Parin810/Farm-Produce-Logging-and-Monitoring-/Final Report/circuit.png

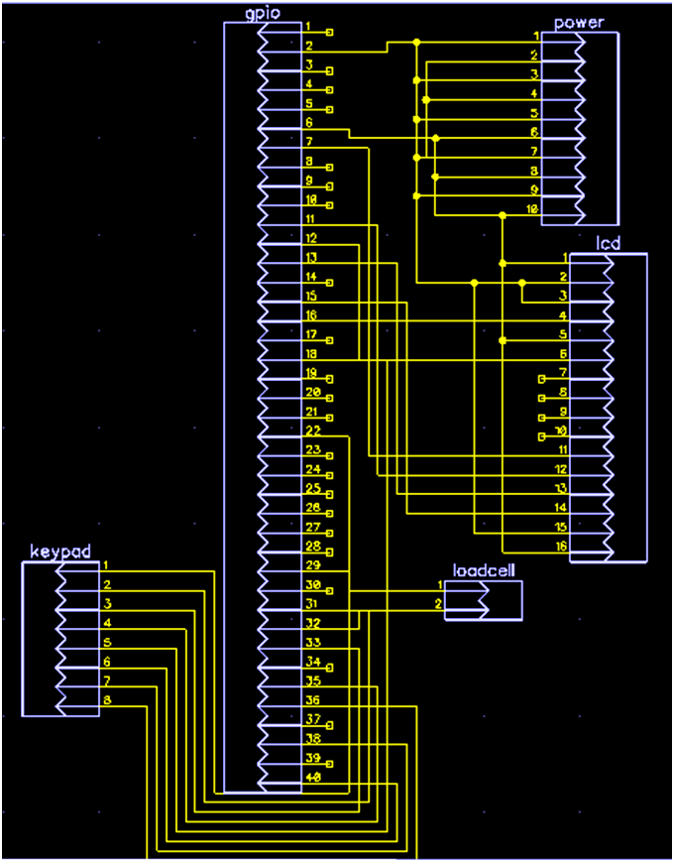
Final Report/circuit.png
