Parin810/Farm-Produce-Logging-and-Monitoring-/Poster/project_farmproduce.png

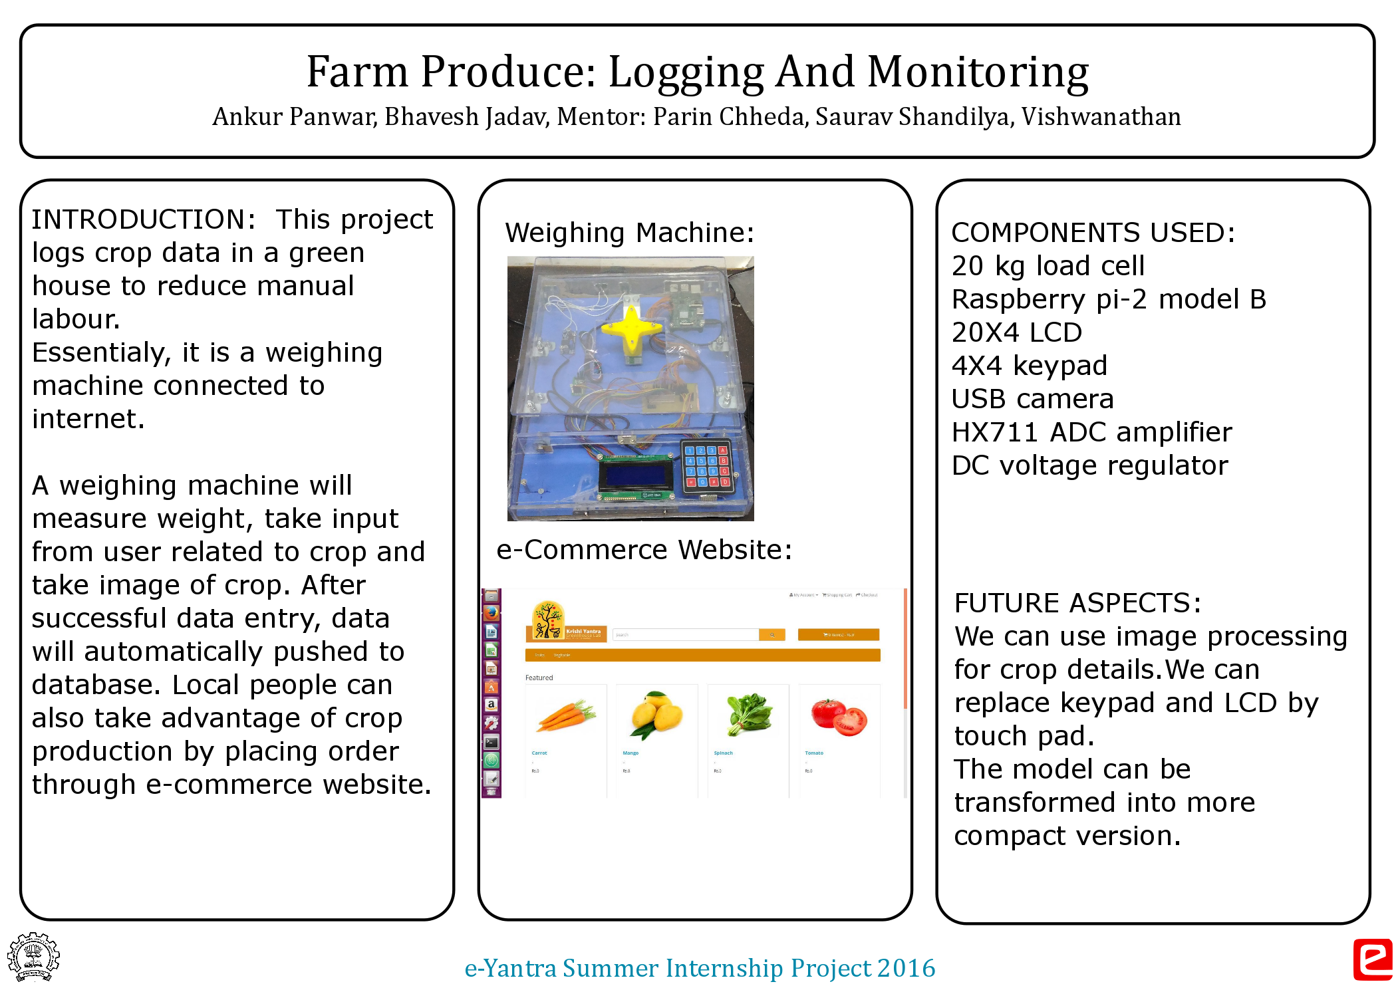
Poster/project_farmproduce.png
