Parin810/Farm-Produce-Logging-and-Monitoring-/progress-presentation-1/lcd.jpg

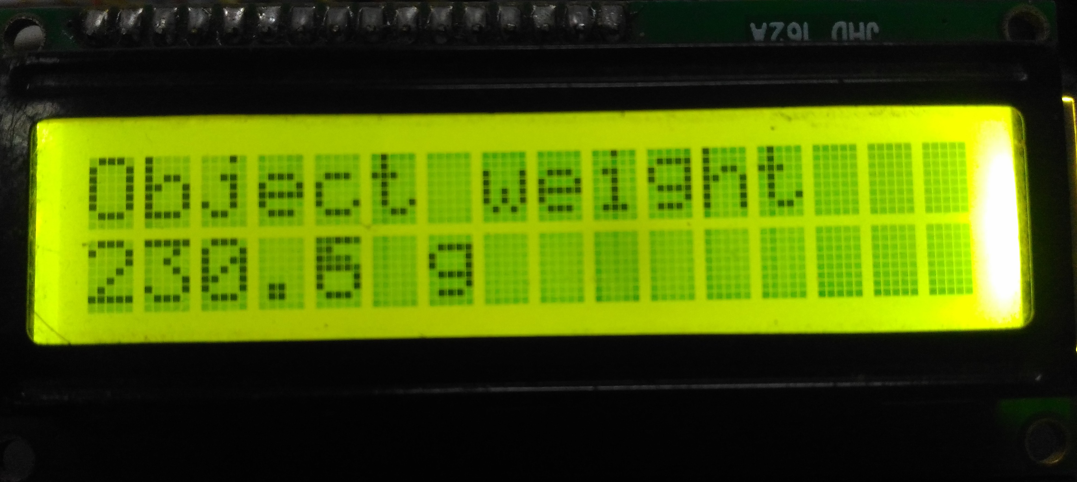
progress-presentation-1/lcd.jpg
