Parin810/Farm-Produce-Logging-and-Monitoring-/progress-presentation-1/load_cell.jpg

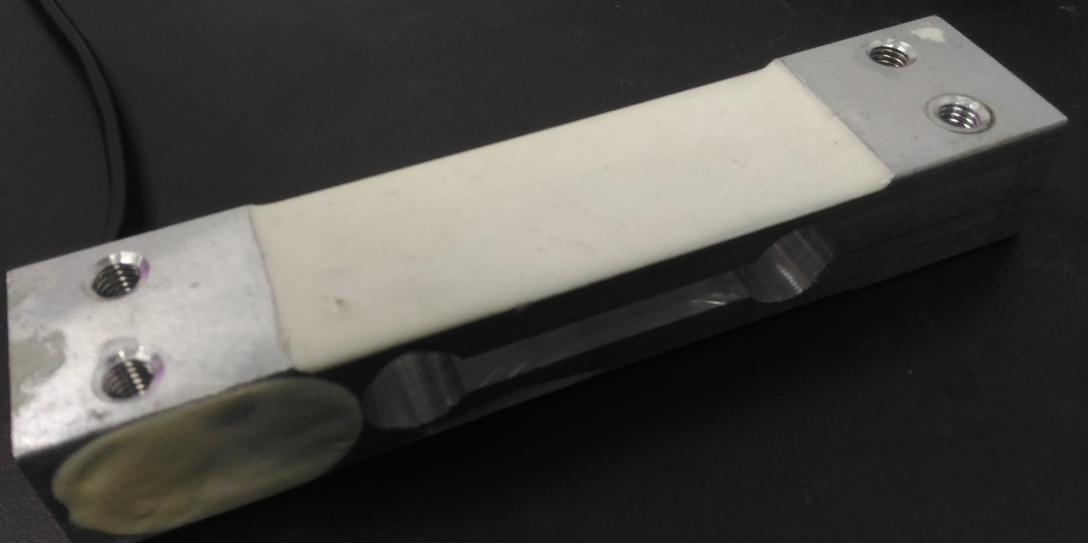
progress-presentation-1/load_cell.jpg
