Parin810/Farm-Produce-Logging-and-Monitoring-/progress-presentation-1/open.jpg

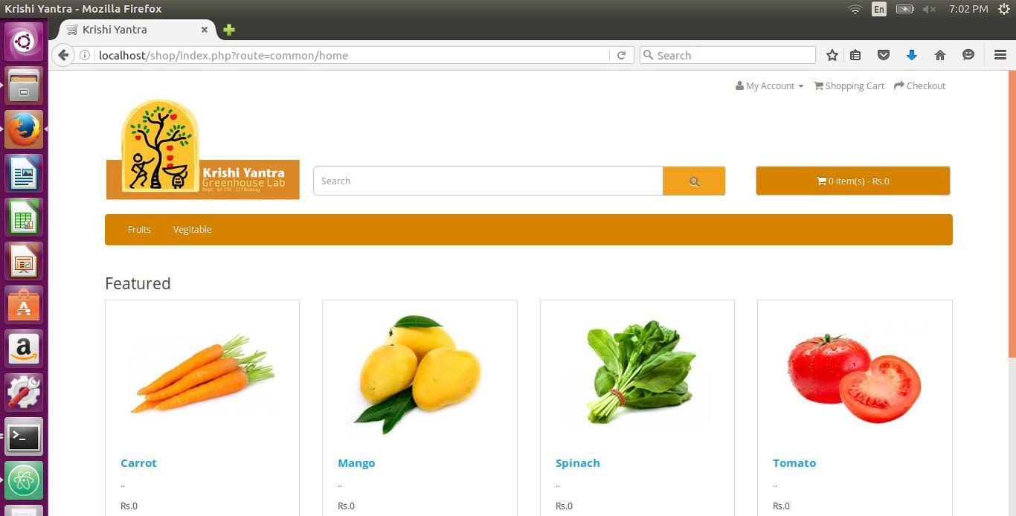
progress-presentation-1/open.jpg
