Parin810/Farm-Produce-Logging-and-Monitoring-/progress-presentation-1/page.jpg

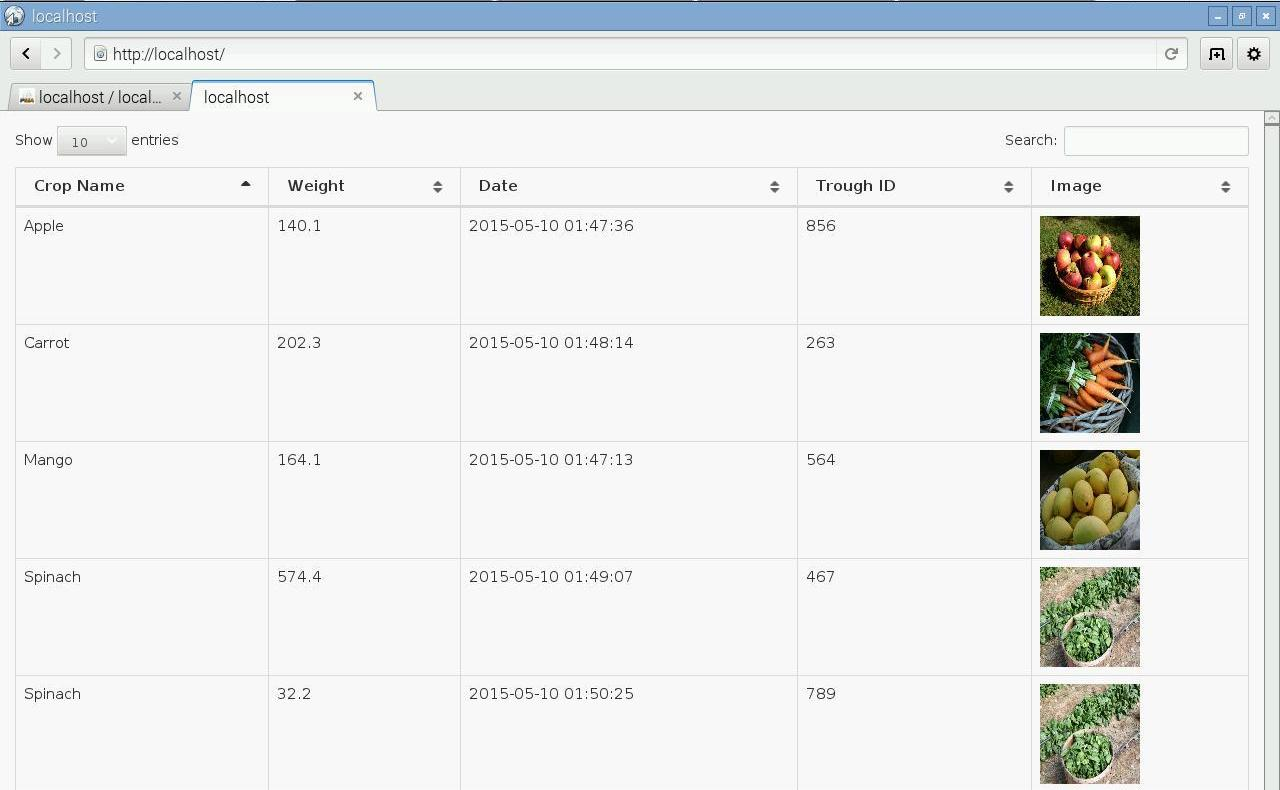
progress-presentation-1/page.jpg
