Parin810/Farm-Produce-Logging-and-Monitoring-/shop/admin/view/javascript/flot/examples/image/hs-2004-27-a-large-web.jpg

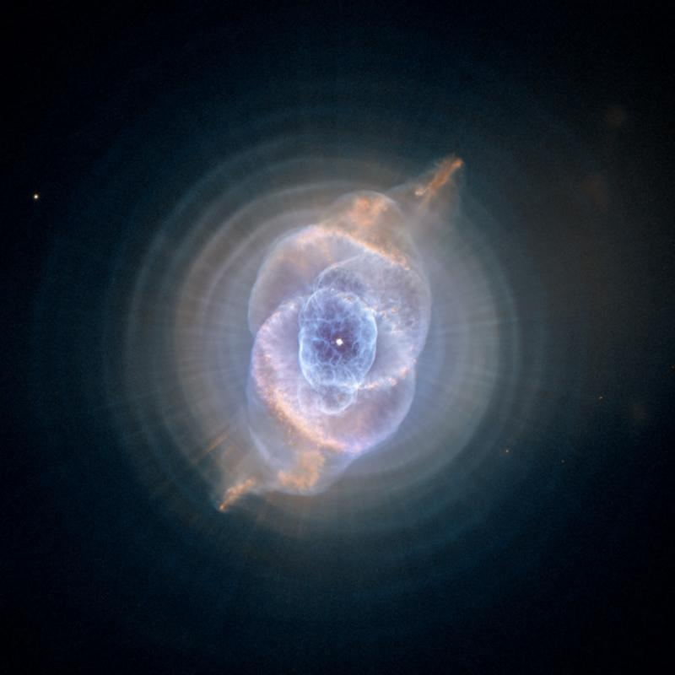
shop/admin/view/javascript/flot/examples/image/hs-2004-27-a-large-web.jpg
