Parin810/Farm-Produce-Logging-and-Monitoring-/shop/catalog/view/theme/default/image/default.png

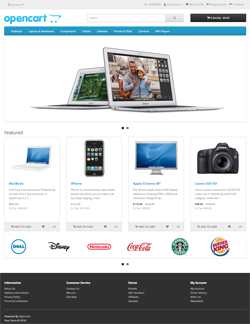
shop/catalog/view/theme/default/image/default.png
