Parin810/Farm-Produce-Logging-and-Monitoring-/shop/image/cache/catalog/demo/apple_cinema_30-200x200.jpg

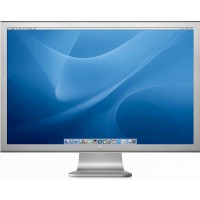
shop/image/cache/catalog/demo/apple_cinema_30-200x200.jpg
