Parin810/Farm-Produce-Logging-and-Monitoring-/shop/image/cache/catalog/demo/canon_eos_5d_1-200x200.jpg

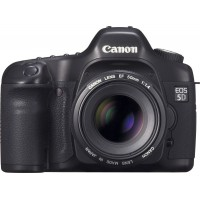
shop/image/cache/catalog/demo/canon_eos_5d_1-200x200.jpg
