Parin810/Farm-Produce-Logging-and-Monitoring-/shop/image/cache/catalog/demo/macbook_1-200x200.jpg

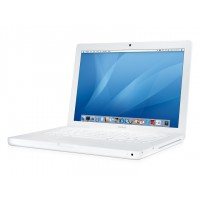
shop/image/cache/catalog/demo/macbook_1-200x200.jpg
