Parin810/Farm-Produce-Logging-and-Monitoring-/shop/image/cache/catalog/mango-200x200.jpeg

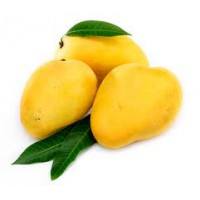
shop/image/cache/catalog/mango-200x200.jpeg
