Parin810/Farm-Produce-Logging-and-Monitoring-/shop/image/cache/catalog/spinach-200x200.jpg

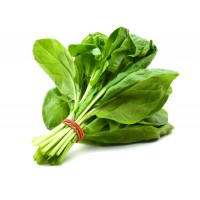
shop/image/cache/catalog/spinach-200x200.jpg
