Parin810/Farm-Produce-Logging-and-Monitoring-/shop/image/cache/placeholder-200x200.png

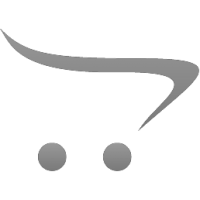
shop/image/cache/placeholder-200x200.png
