Parin810/Farm-Produce-Logging-and-Monitoring-/shop/image/catalog/carrot.jpg

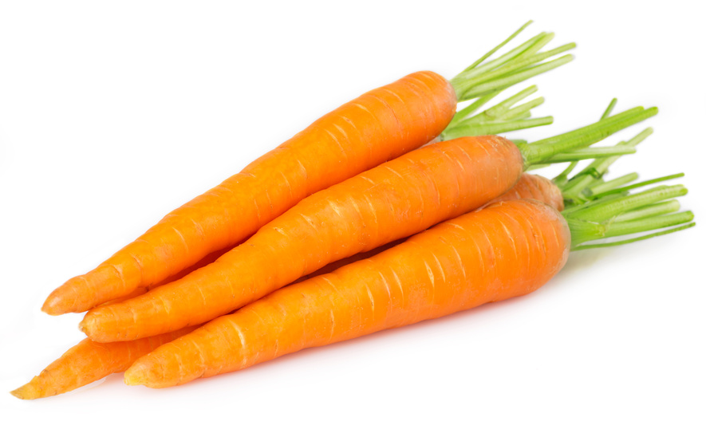
shop/image/catalog/carrot.jpg
