Parin810/Farm-Produce-Logging-and-Monitoring-/shop/image/catalog/demo/apple_cinema_30.jpg

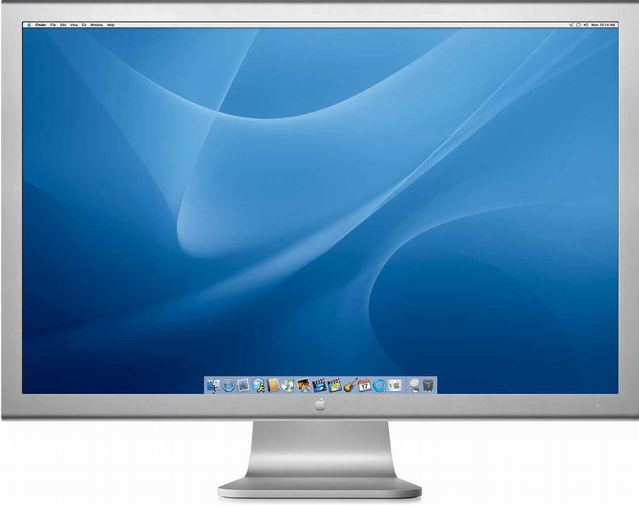
shop/image/catalog/demo/apple_cinema_30.jpg
