Parin810/Farm-Produce-Logging-and-Monitoring-/shop/image/catalog/demo/canon_eos_5d_2.jpg

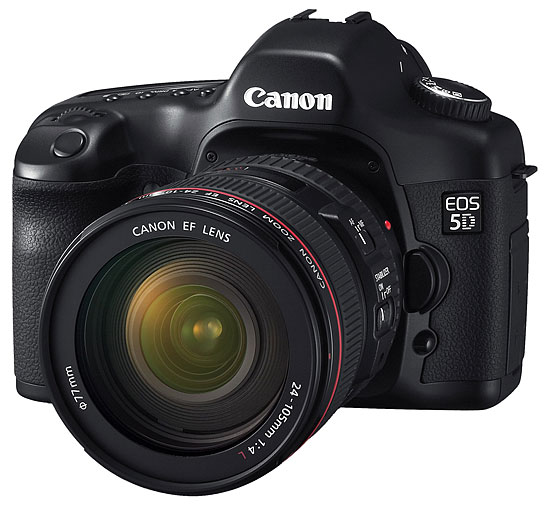
shop/image/catalog/demo/canon_eos_5d_2.jpg
