Parin810/Farm-Produce-Logging-and-Monitoring-/shop/image/catalog/demo/compaq_presario.jpg

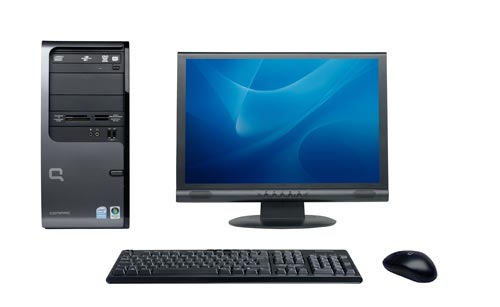
shop/image/catalog/demo/compaq_presario.jpg
