Parin810/Farm-Produce-Logging-and-Monitoring-/shop/image/catalog/demo/gift-voucher-birthday.jpg

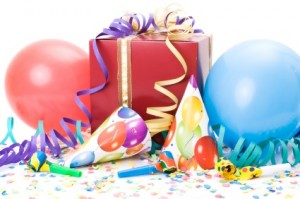
shop/image/catalog/demo/gift-voucher-birthday.jpg
