Parin810/Farm-Produce-Logging-and-Monitoring-/shop/image/catalog/demo/hp_1.jpg

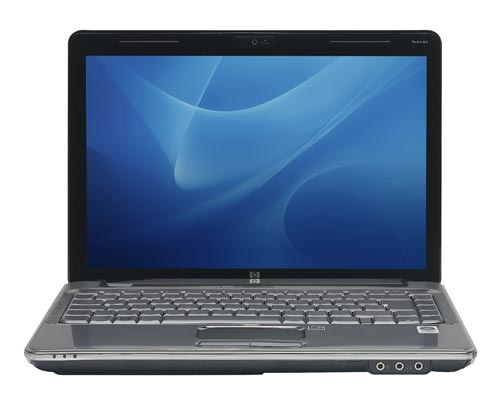
shop/image/catalog/demo/hp_1.jpg
