Parin810/Farm-Produce-Logging-and-Monitoring-/shop/image/catalog/demo/hp_2.jpg

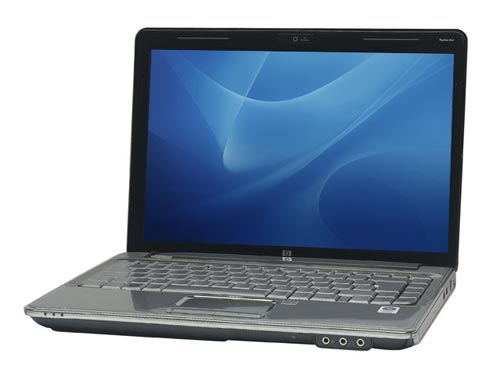
shop/image/catalog/demo/hp_2.jpg
