Parin810/Farm-Produce-Logging-and-Monitoring-/shop/image/catalog/demo/hp_3.jpg

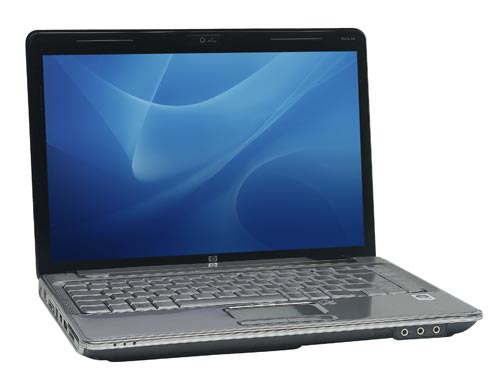
shop/image/catalog/demo/hp_3.jpg
