Parin810/Farm-Produce-Logging-and-Monitoring-/shop/image/catalog/demo/htc_touch_hd_1.jpg

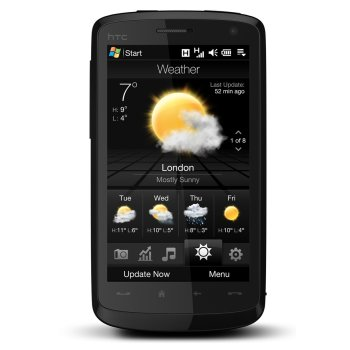
shop/image/catalog/demo/htc_touch_hd_1.jpg
