Parin810/Farm-Produce-Logging-and-Monitoring-/shop/image/catalog/demo/imac_1.jpg

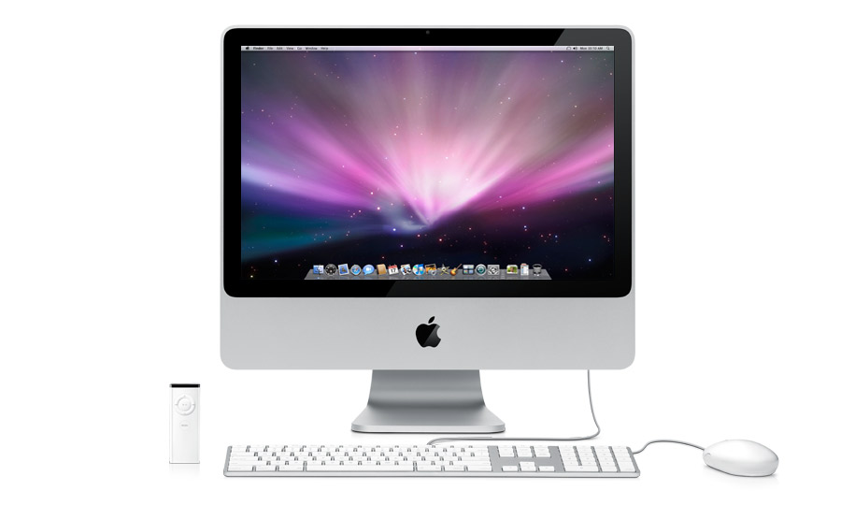
shop/image/catalog/demo/imac_1.jpg
