Parin810/Farm-Produce-Logging-and-Monitoring-/shop/image/catalog/demo/ipod_classic_3.jpg

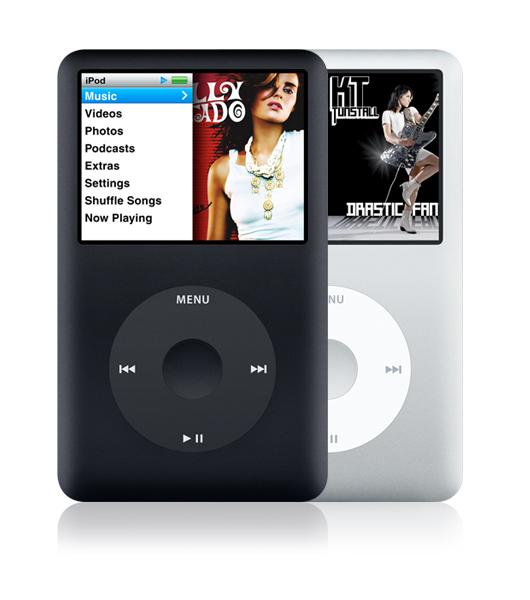
shop/image/catalog/demo/ipod_classic_3.jpg
