Parin810/Farm-Produce-Logging-and-Monitoring-/shop/image/catalog/demo/ipod_shuffle_1.jpg

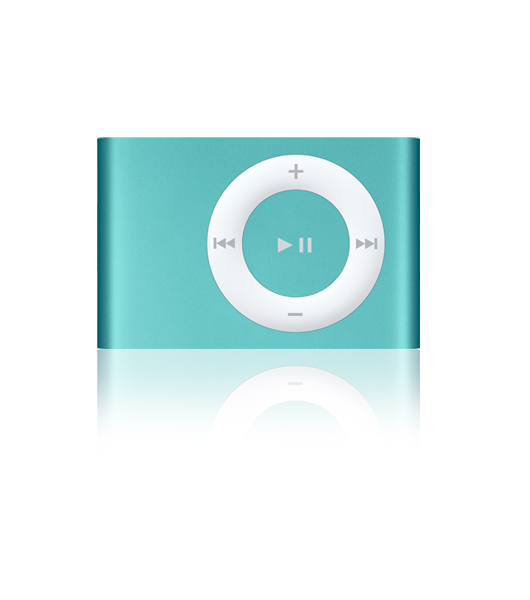
shop/image/catalog/demo/ipod_shuffle_1.jpg
