Parin810/Farm-Produce-Logging-and-Monitoring-/shop/image/catalog/demo/ipod_touch_4.jpg

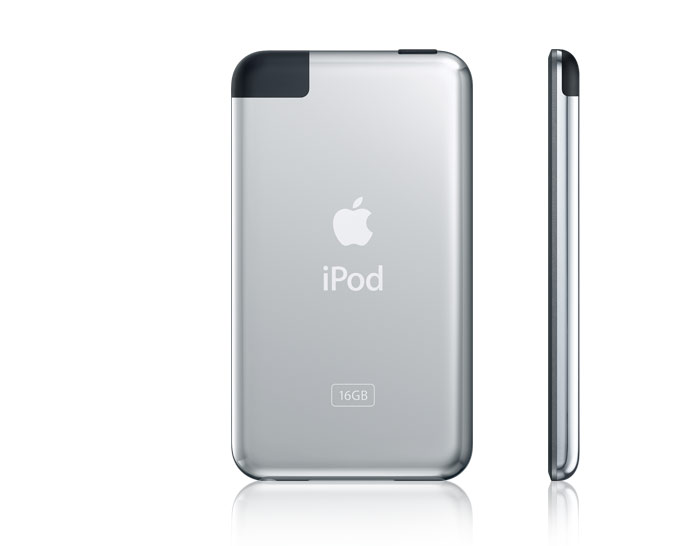
shop/image/catalog/demo/ipod_touch_4.jpg
