Parin810/Farm-Produce-Logging-and-Monitoring-/shop/image/catalog/demo/macbook_3.jpg

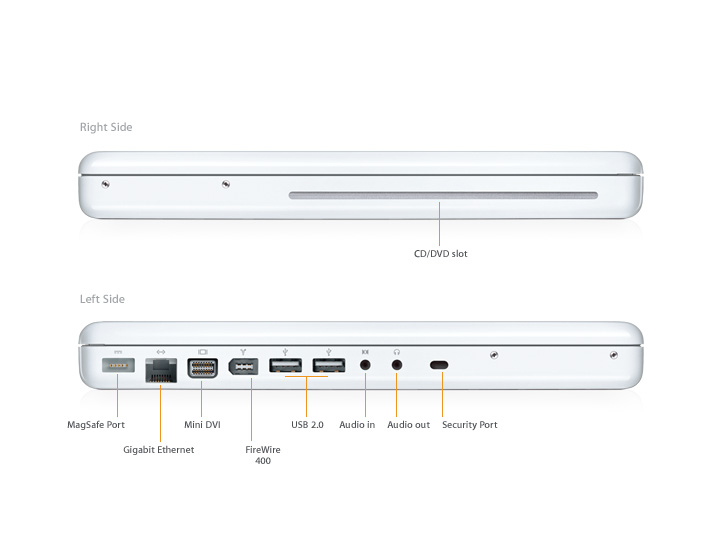
shop/image/catalog/demo/macbook_3.jpg
