Parin810/Farm-Produce-Logging-and-Monitoring-/shop/image/catalog/demo/macbook_4.jpg

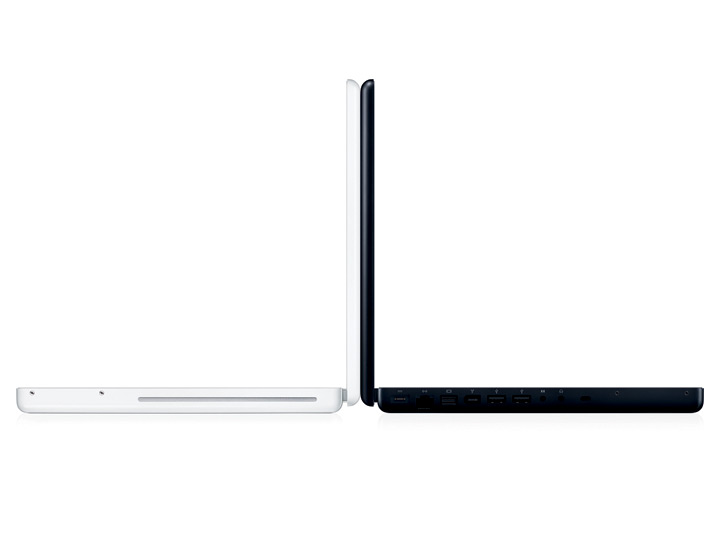
shop/image/catalog/demo/macbook_4.jpg
