Parin810/Farm-Produce-Logging-and-Monitoring-/shop/image/catalog/demo/macbook_air_2.jpg

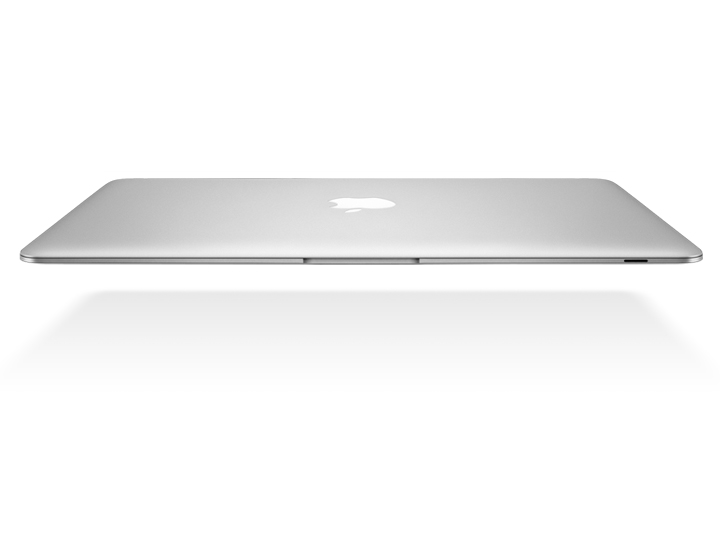
shop/image/catalog/demo/macbook_air_2.jpg
