Parin810/Farm-Produce-Logging-and-Monitoring-/shop/image/catalog/demo/macbook_air_3.jpg

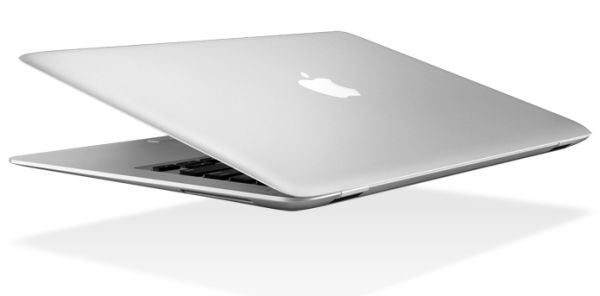
shop/image/catalog/demo/macbook_air_3.jpg
