Parin810/Farm-Produce-Logging-and-Monitoring-/shop/image/catalog/demo/macbook_pro_1.jpg

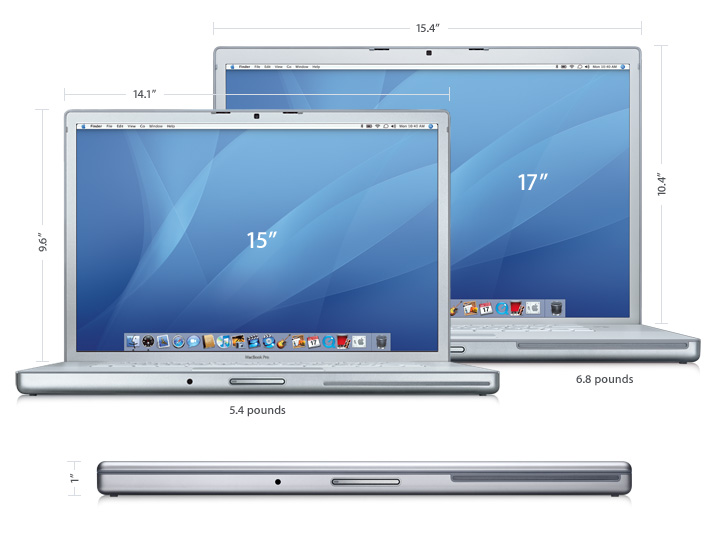
shop/image/catalog/demo/macbook_pro_1.jpg
