Parin810/Farm-Produce-Logging-and-Monitoring-/shop/image/catalog/demo/nikon_d300_3.jpg

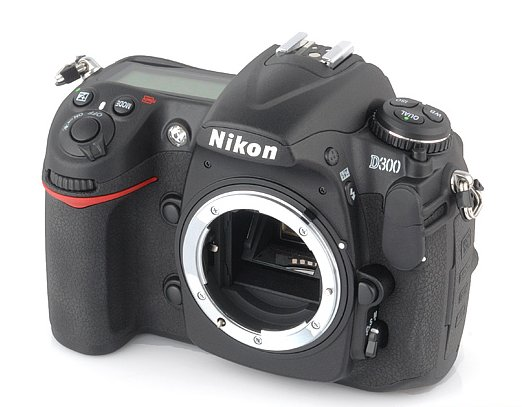
shop/image/catalog/demo/nikon_d300_3.jpg
