Parin810/Farm-Produce-Logging-and-Monitoring-/shop/image/catalog/demo/nikon_d300_4.jpg

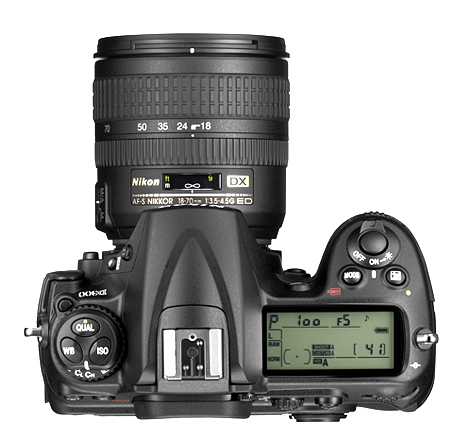
shop/image/catalog/demo/nikon_d300_4.jpg
