Parin810/Farm-Produce-Logging-and-Monitoring-/shop/image/catalog/demo/palm_treo_pro_2.jpg

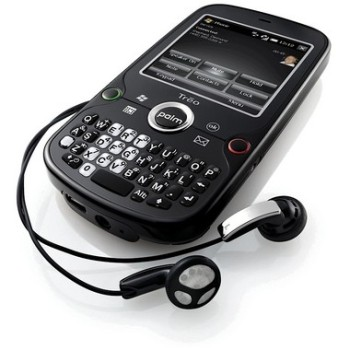
shop/image/catalog/demo/palm_treo_pro_2.jpg
