Parin810/Farm-Produce-Logging-and-Monitoring-/shop/image/catalog/demo/product/iphone.jpg

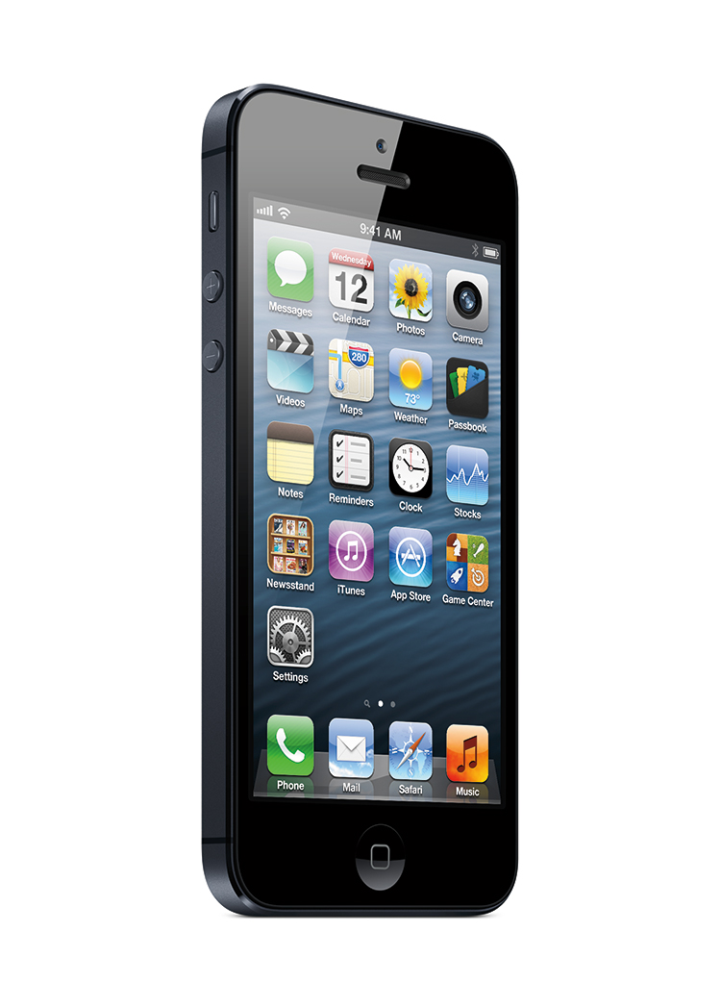
shop/image/catalog/demo/product/iphone.jpg
