Parin810/Farm-Produce-Logging-and-Monitoring-/shop/image/catalog/demo/product/macbook.jpg

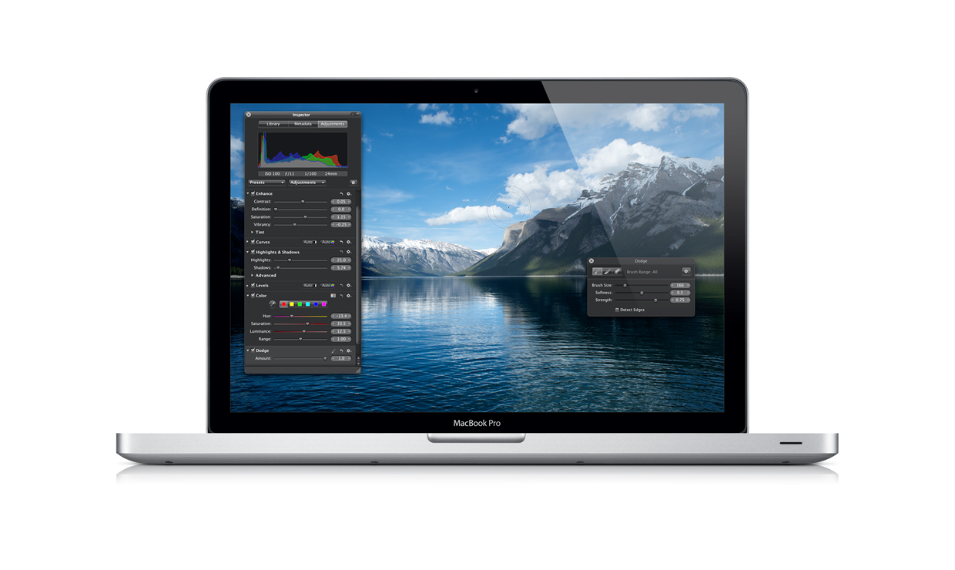
shop/image/catalog/demo/product/macbook.jpg
