Parin810/Farm-Produce-Logging-and-Monitoring-/shop/image/catalog/demo/product/samsungtab.jpg

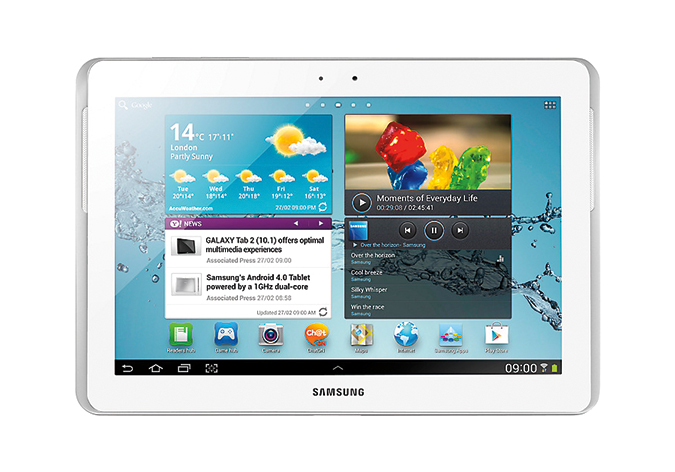
shop/image/catalog/demo/product/samsungtab.jpg
