Parin810/Farm-Produce-Logging-and-Monitoring-/shop/image/catalog/demo/product/thunderboltdisplay.jpg

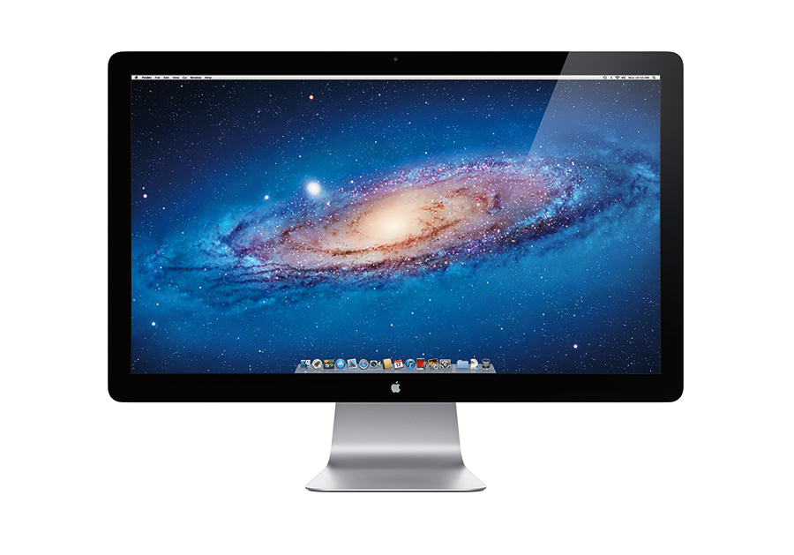
shop/image/catalog/demo/product/thunderboltdisplay.jpg
