Parin810/Farm-Produce-Logging-and-Monitoring-/shop/image/catalog/demo/samsung_syncmaster_941bw.jpg

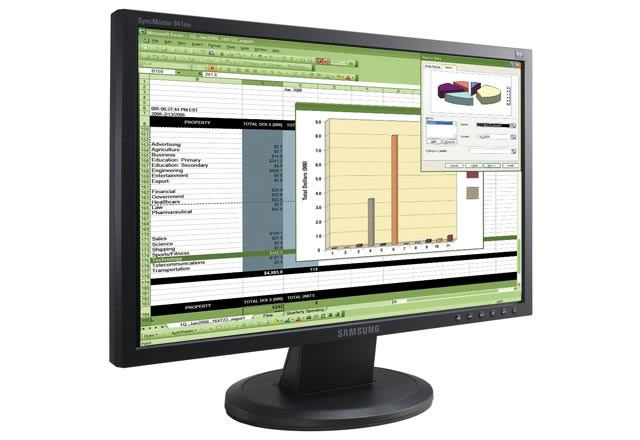
shop/image/catalog/demo/samsung_syncmaster_941bw.jpg
