Parin810/Farm-Produce-Logging-and-Monitoring-/shop/image/catalog/demo/samsung_tab_2.jpg

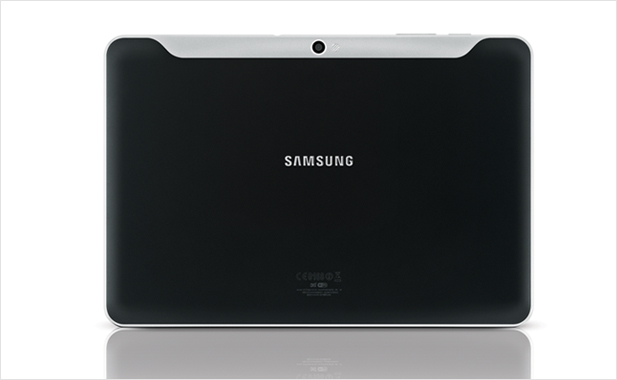
shop/image/catalog/demo/samsung_tab_2.jpg
