Parin810/Farm-Produce-Logging-and-Monitoring-/shop/image/catalog/demo/sony_vaio_2.jpg

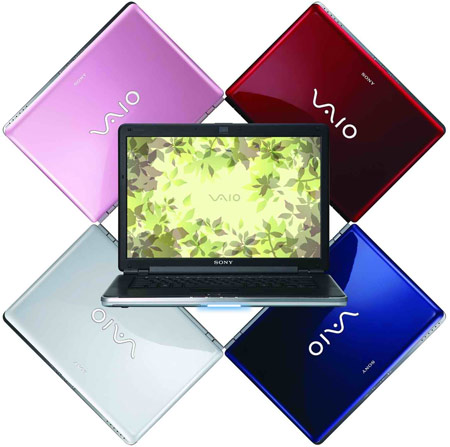
shop/image/catalog/demo/sony_vaio_2.jpg
