Parin810/Farm-Produce-Logging-and-Monitoring-/shop/image/catalog/KrishiYantra02.jpg

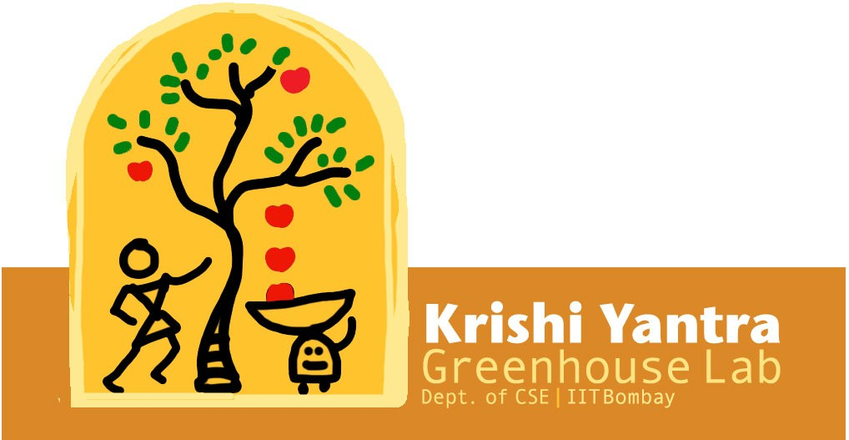
shop/image/catalog/KrishiYantra02.jpg
