Parin810/Farm-Produce-Logging-and-Monitoring-/shop/image/catalog/mango.jpeg

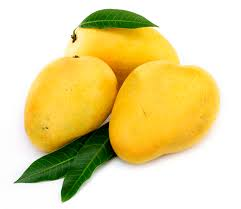
shop/image/catalog/mango.jpeg
