Parin810/Farm-Produce-Logging-and-Monitoring-/shop/image/catalog/spinach.jpg

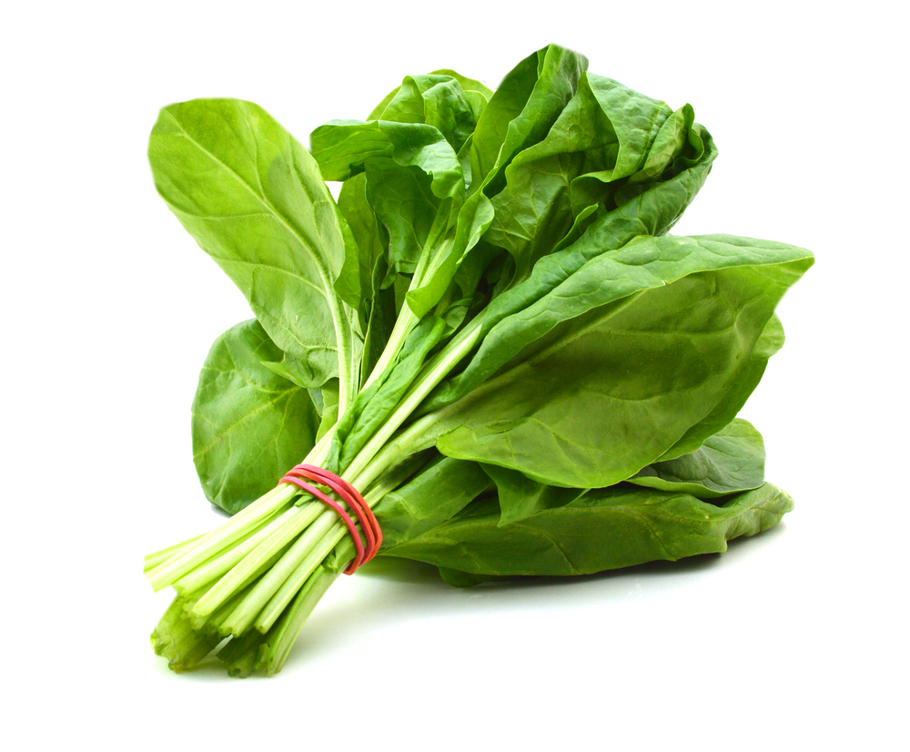
shop/image/catalog/spinach.jpg
