Parin810/Farm-Produce-Logging-and-Monitoring-/shop/image/catalog/tomato.jpeg

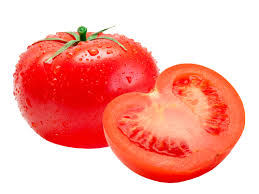
shop/image/catalog/tomato.jpeg
