Parin810/Farm-Produce-Logging-and-Monitoring-/shop/image/no_image.png

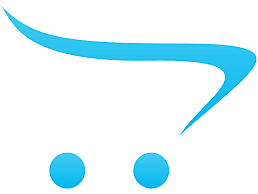
shop/image/no_image.png
