Parin810/Farm-Produce-Logging-and-Monitoring-/Weighing Machine Design/kpad/keypad-16keymembrane.jpg

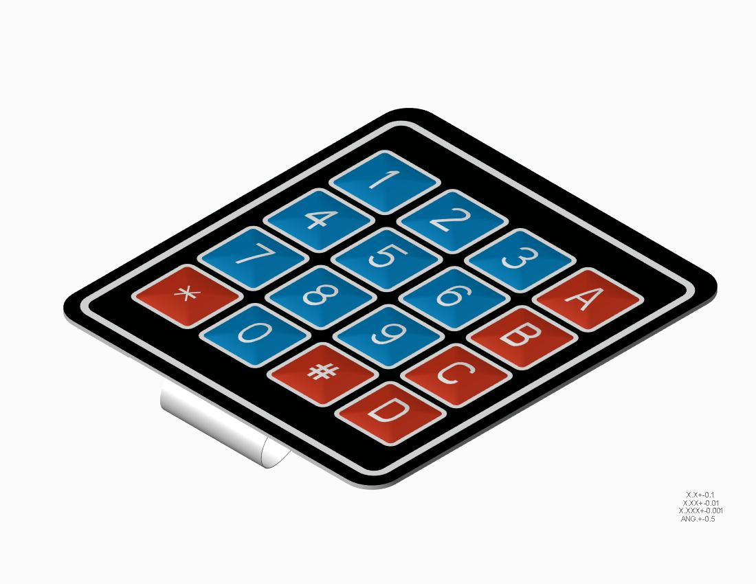
Weighing Machine Design/kpad/keypad-16keymembrane.jpg
