Parin810/Farm-Produce-Logging-and-Monitoring-/Weighing Machine Design/lcd/20X4LCD JHD204A.JPG

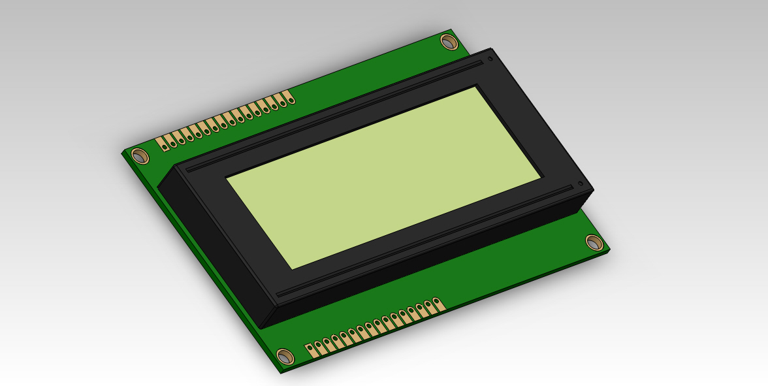
Weighing Machine Design/lcd/20X4LCD JHD204A.JPG
