Parin810/Farm-Produce-Logging-and-Monitoring-/Weighing Machine Design/pic1.JPG

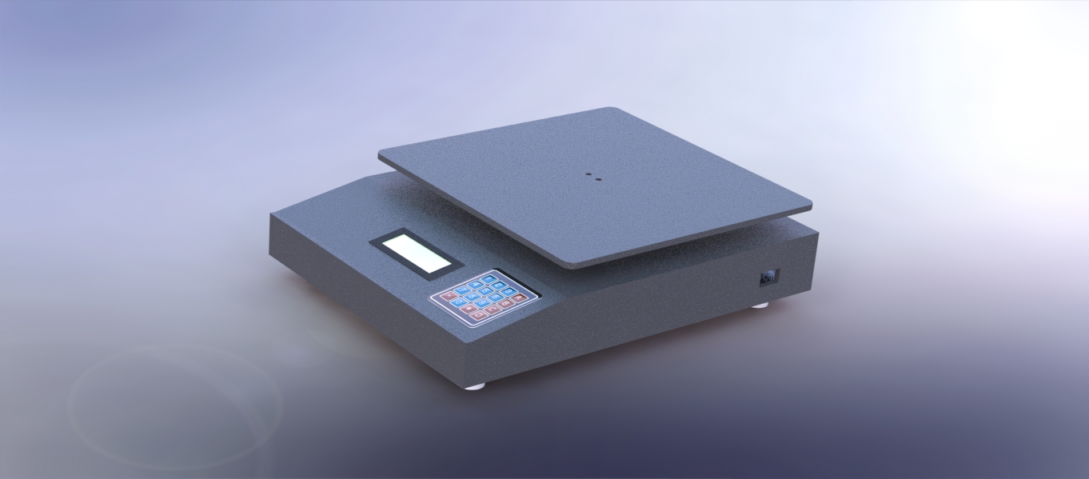
Weighing Machine Design/pic1.JPG
