Parin810/Farm-Produce-Logging-and-Monitoring-/Weighing Machine Design/pic2.JPG

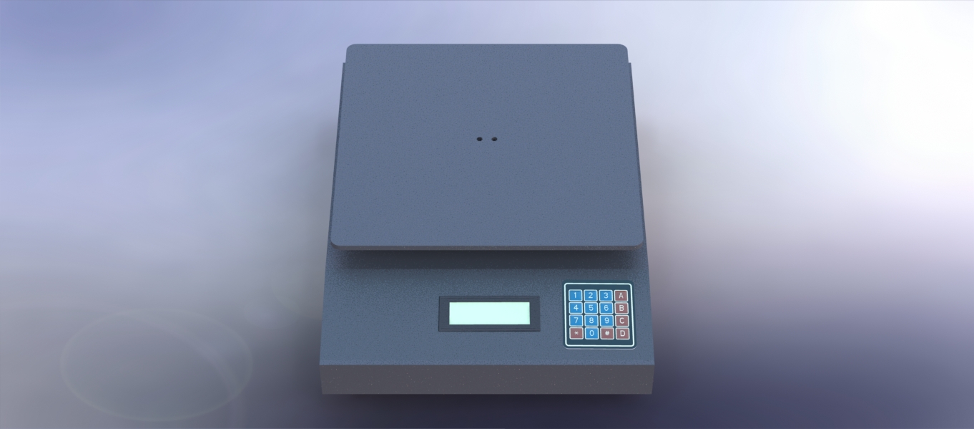
Weighing Machine Design/pic2.JPG
