Parin810/Farm-Produce-Logging-and-Monitoring-/Weighing Machine Design/pic3.JPG

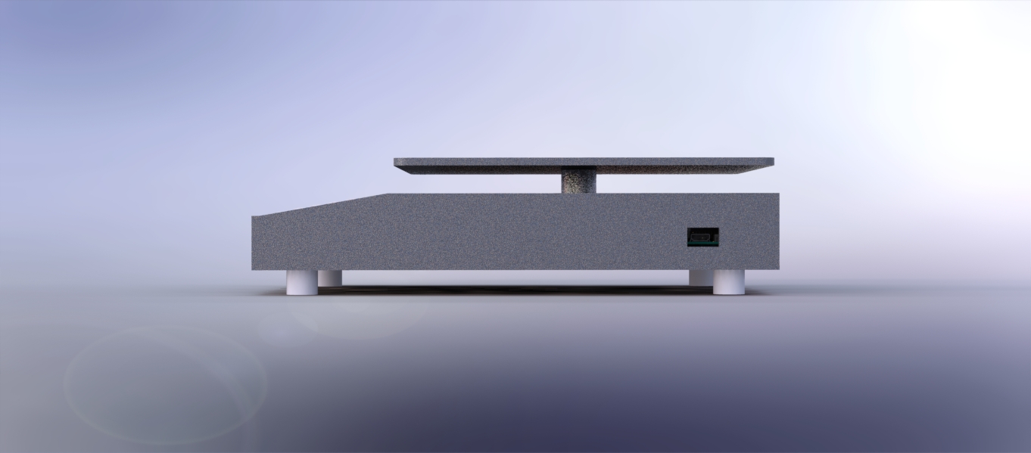
Weighing Machine Design/pic3.JPG
