Parin810/Farm-Produce-Logging-and-Monitoring-/Weighing Machine Design/pic4.JPG

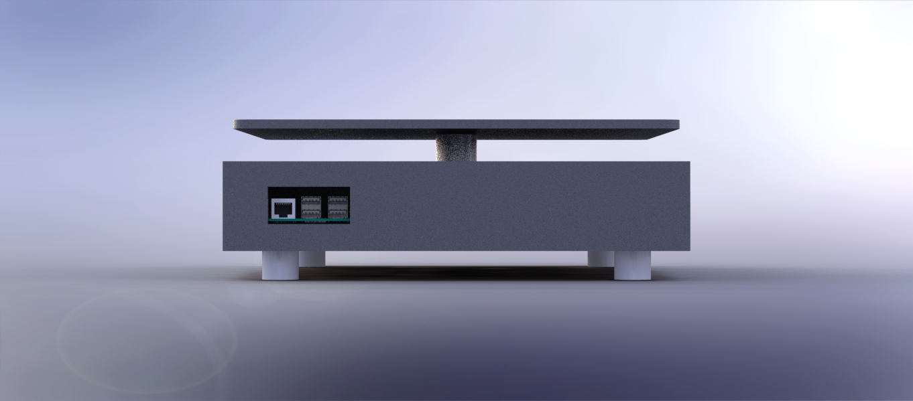
Weighing Machine Design/pic4.JPG
