Parin810/Farm-Produce-Logging-and-Monitoring-/Weighing Machine Design/pic5.JPG

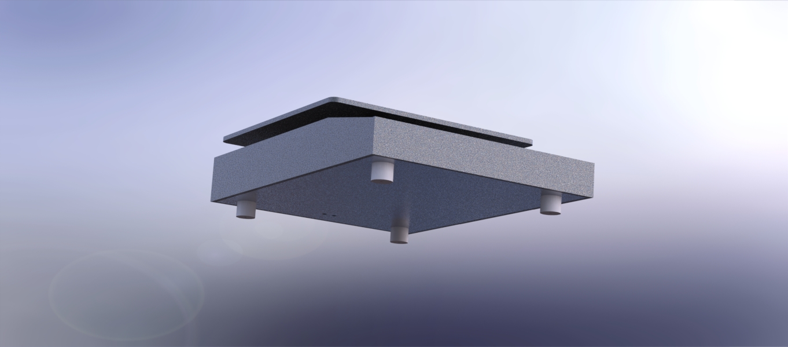
Weighing Machine Design/pic5.JPG
