Parin810/Farm-Produce-Logging-and-Monitoring-/Weighing Machine Design/rpi/@raspberry_pi_model_B+_bot_2.jpg

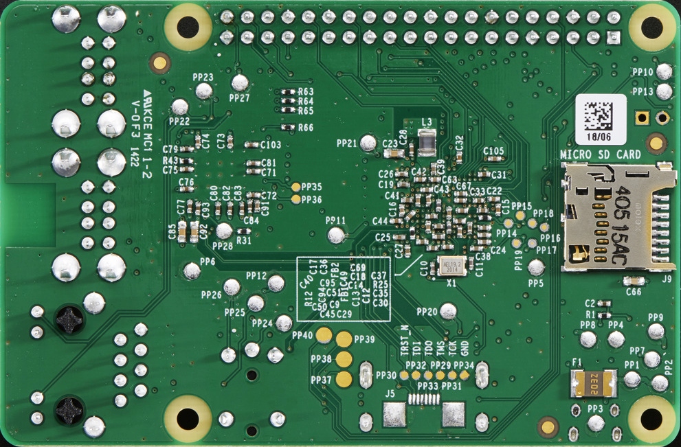
Weighing Machine Design/rpi/@raspberry_pi_model_B+_bot_2.jpg
