Parin810/Farm-Produce-Logging-and-Monitoring-/Weighing Machine Design/rpi/@raspberry_pi_model_B+_top_1.jpg

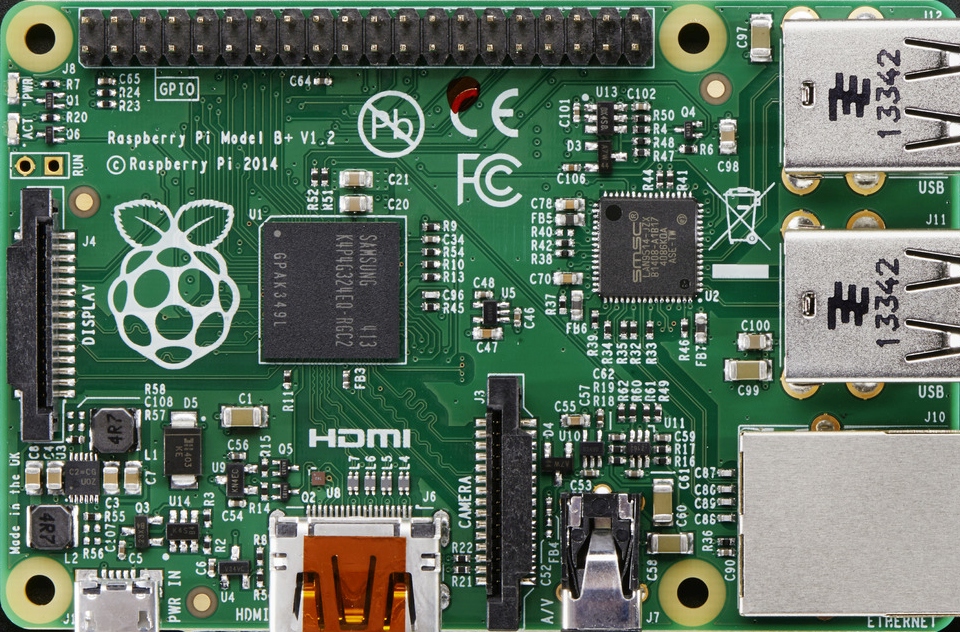
Weighing Machine Design/rpi/@raspberry_pi_model_B+_top_1.jpg
