Parin810/Farm-Produce-Logging-and-Monitoring-/Weighing Machine Design/rpi/mechanicalspecB+.png

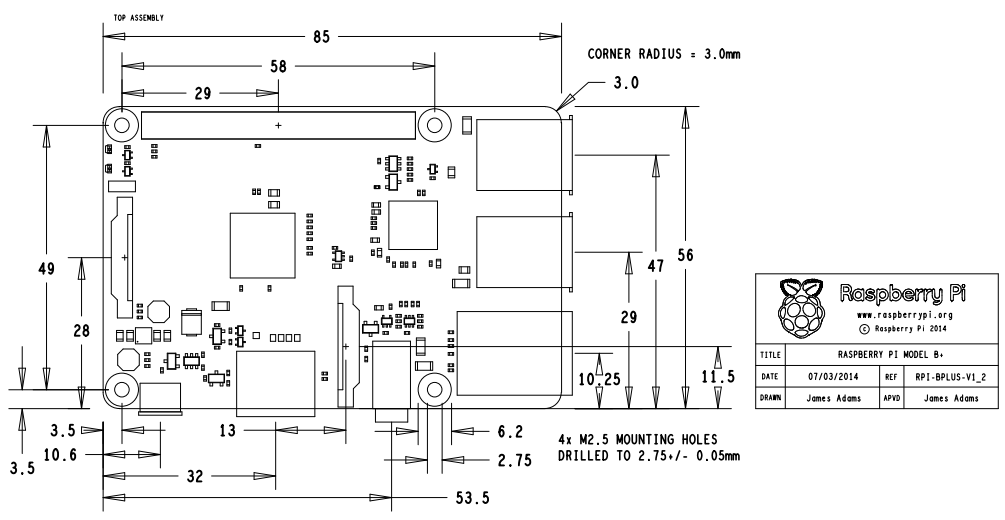
Weighing Machine Design/rpi/mechanicalspecB+.png
