Parin810/Farm-Produce-Logging-and-Monitoring-/Weighing Machine Design/rpi/raspberry_pi_B+_(RENDER2).JPG

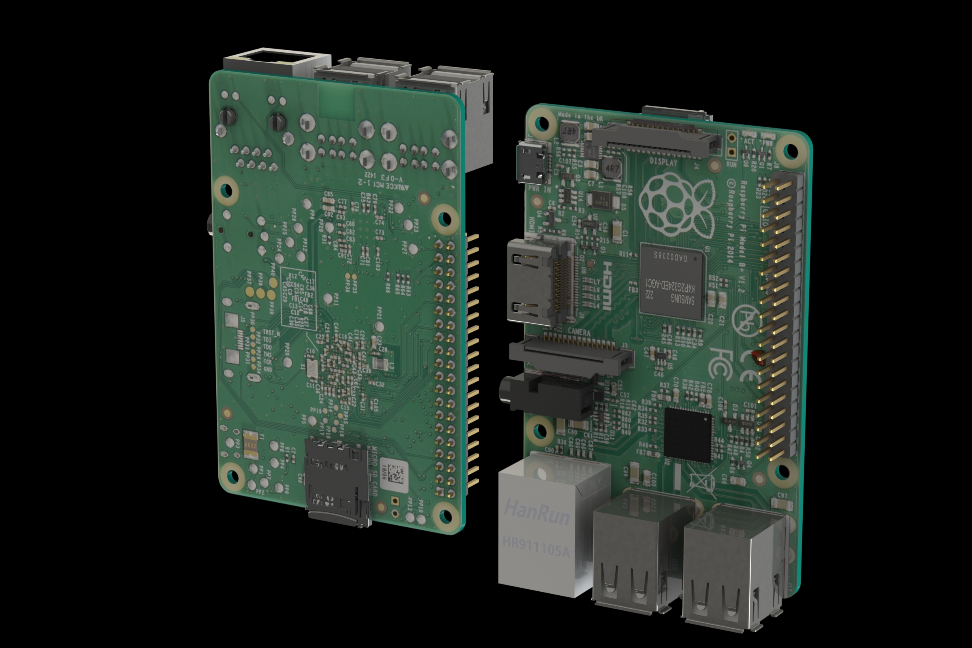
Weighing Machine Design/rpi/raspberry_pi_B+_(RENDER2).JPG
