Parin810/Farm-Produce-Logging-and-Monitoring-/Weighing Machine Design/lasercut/plate3.DXF

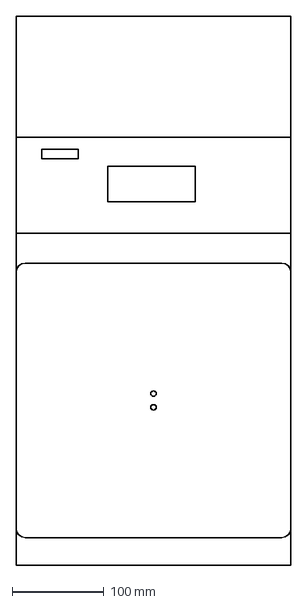
[picture p157: CAD file, 2017-04-19]
Weighing Machine Design/lasercut/plate3.DXF
300.0 x 600.0 mm
