Parin810/Farm-Produce-Logging-and-Monitoring-/Weighing Machine Design/lcd/20X4LCD JHD204A.STEP

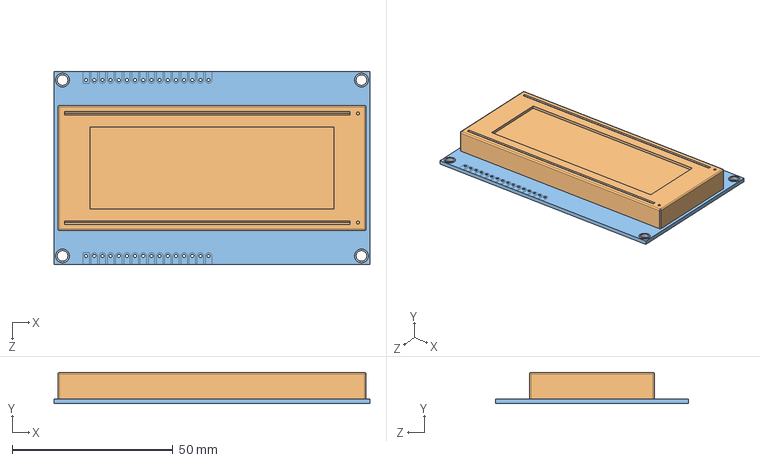
[picture p158: CAD file, 2017-04-19]
Weighing Machine Design/lcd/20X4LCD JHD204A.STEP
98.3 x 9.76 x 60.0 mm
