Parin810/Farm-Produce-Logging-and-Monitoring-/Weighing Machine Design/loadcell.SLDPRT

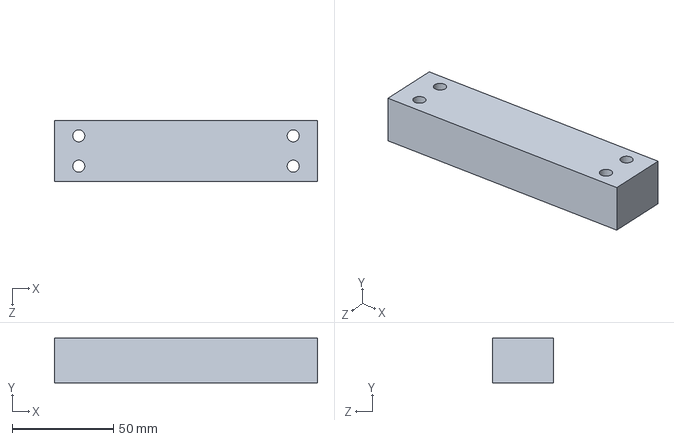
[picture p159: CAD file, 2017-04-19]
Weighing Machine Design/loadcell.SLDPRT
130.0 x 22.0 x 30.0 mm
