Parin810/Farm-Produce-Logging-and-Monitoring-/Weighing Machine Design/frontpanelcut.SLDPRT

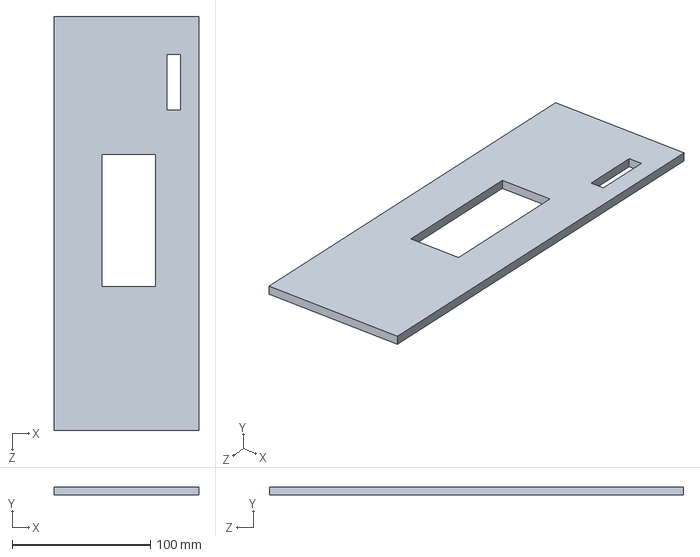
[picture p160: CAD file, 2017-04-19]
Weighing Machine Design/frontpanelcut.SLDPRT
105.0 x 6.00 x 300.0 mm
