Parin810/Farm-Produce-Logging-and-Monitoring-/Weighing Machine Design/lasercut/plate1.DXF

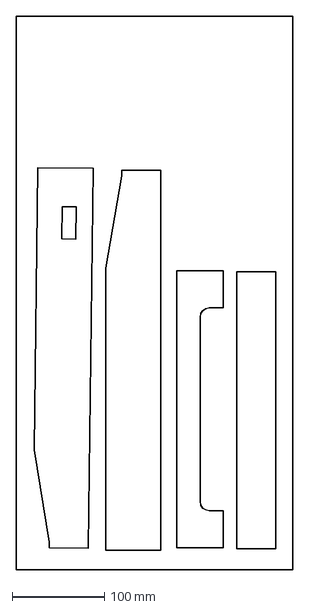
[picture p161: CAD file, 2017-04-19]
Weighing Machine Design/lasercut/plate1.DXF
300.0 x 600.0 mm
