Parin810/Farm-Produce-Logging-and-Monitoring-/Weighing Machine Design/rpi/raspberry_pi_B+_(audio_video2).SLDPRT

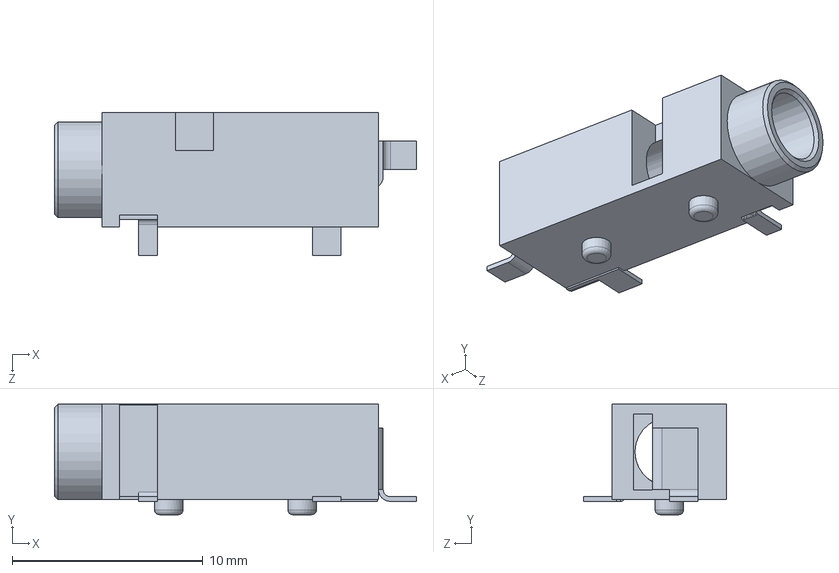
[picture p163: CAD file, 2017-04-19]
Weighing Machine Design/rpi/raspberry_pi_B+_(audio_video2).SLDPRT
19.0 x 5.80 x 7.50 mm
