Parin810/Farm-Produce-Logging-and-Monitoring-/Weighing Machine Design/rpi/raspberry_pi_B+_(RJ45).SLDPRT

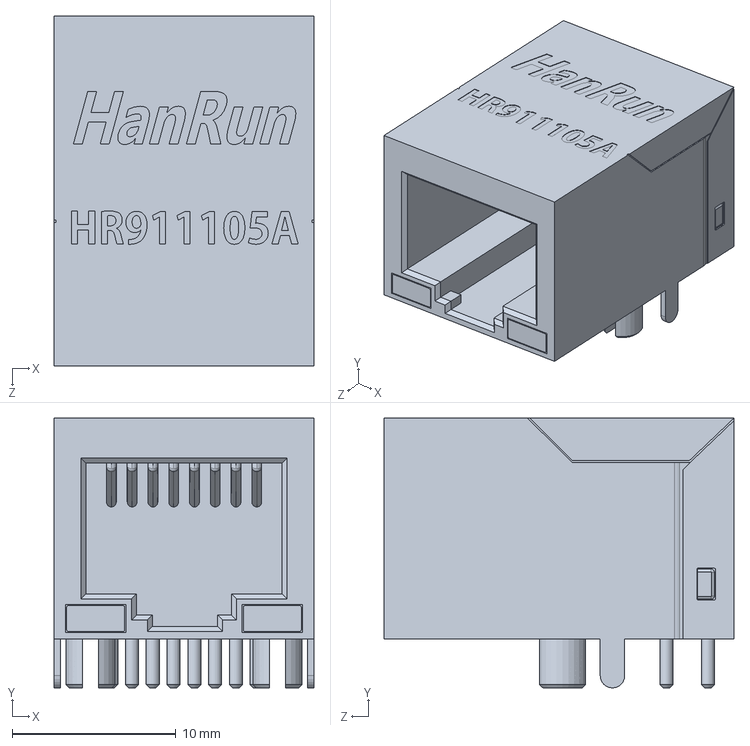
[picture p164: CAD file, 2017-04-19]
Weighing Machine Design/rpi/raspberry_pi_B+_(RJ45).SLDPRT
15.9 x 16.5 x 21.4 mm
