Parin810/Farm-Produce-Logging-and-Monitoring-/Weighing Machine Design/sidepanels2.SLDPRT

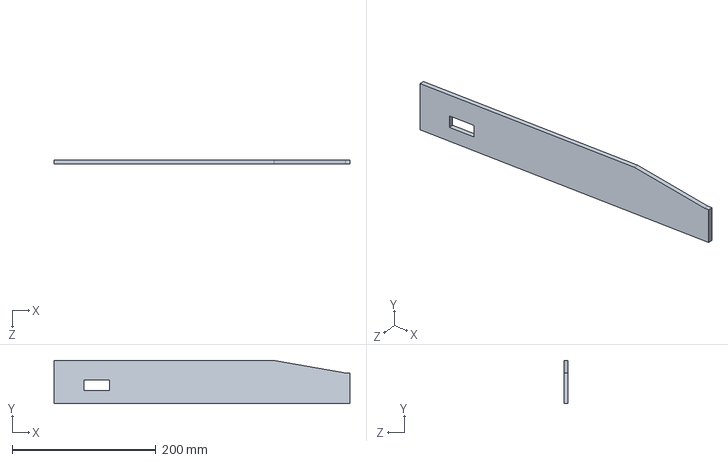
[picture p166: CAD file, 2017-04-19]
Weighing Machine Design/sidepanels2.SLDPRT
412.0 x 60.0 x 6.00 mm
