Parin810/Farm-Produce-Logging-and-Monitoring-/Weighing Machine Design/FrontPanel.SLDPRT

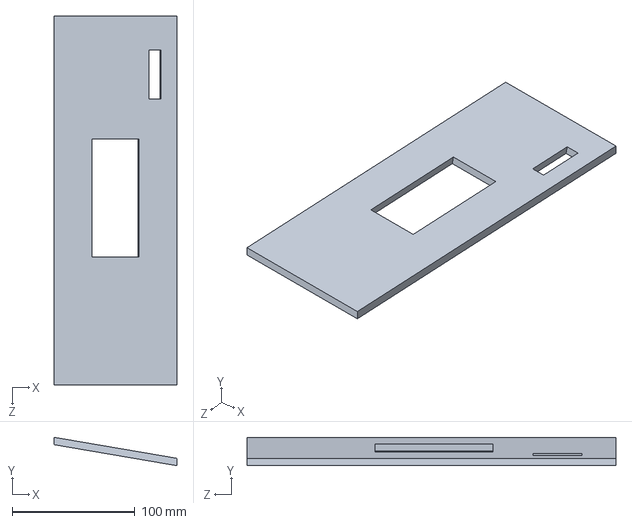
[picture p167: CAD file, 2017-04-19]
Weighing Machine Design/FrontPanel.SLDPRT
100.0 x 23.1 x 300.0 mm
