Parin810/Farm-Produce-Logging-and-Monitoring-/Weighing Machine Design/rpi/raspberry_pi_B+_(168_FBGA_12x12).SLDPRT

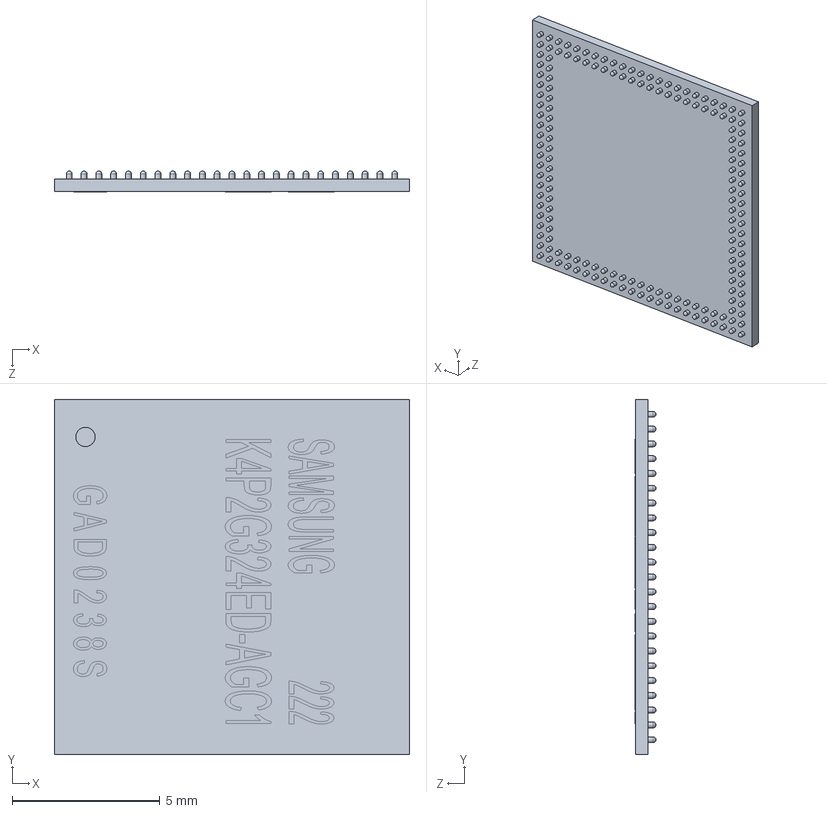
[picture p168: CAD file, 2017-04-19]
Weighing Machine Design/rpi/raspberry_pi_B+_(168_FBGA_12x12).SLDPRT
12.0 x 12.0 x 0.71 mm
