Parin810/Farm-Produce-Logging-and-Monitoring-/Weighing Machine Design/basecylinder.SLDPRT

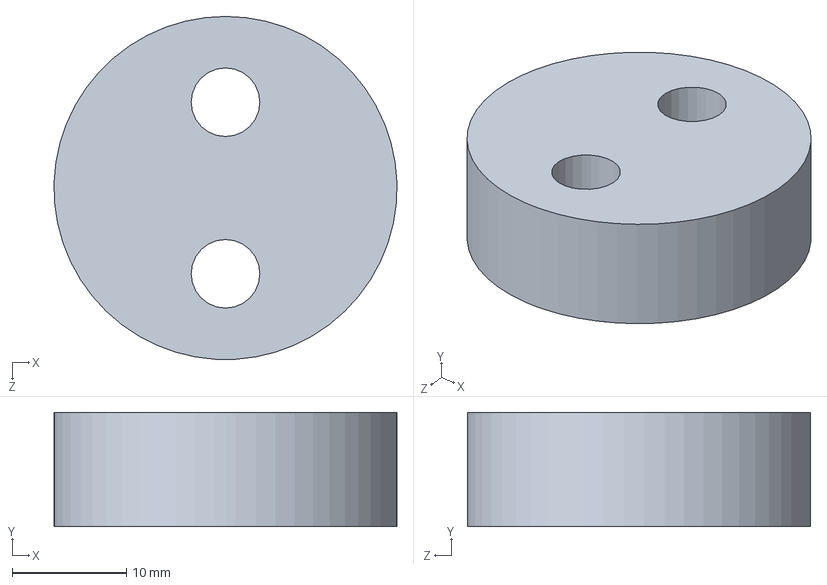
[picture p169: CAD file, 2017-04-19]
Weighing Machine Design/basecylinder.SLDPRT
30.0 x 10.0 x 30.0 mm
