Parin810/Farm-Produce-Logging-and-Monitoring-/Weighing Machine Design/rpi/raspberry_pi_B+_(CI_Board).SLDPRT

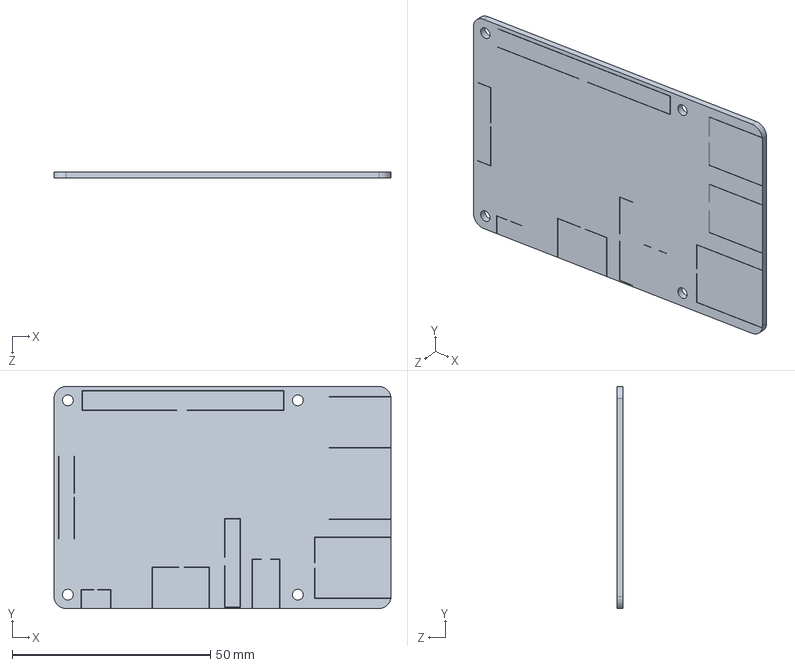
[picture p170: CAD file, 2017-04-19]
Weighing Machine Design/rpi/raspberry_pi_B+_(CI_Board).SLDPRT
85.0 x 56.0 x 1.60 mm
