Parin810/Farm-Produce-Logging-and-Monitoring-/Weighing Machine Design/rpi/raspberry_pi_B+_(microsd2).SLDPRT

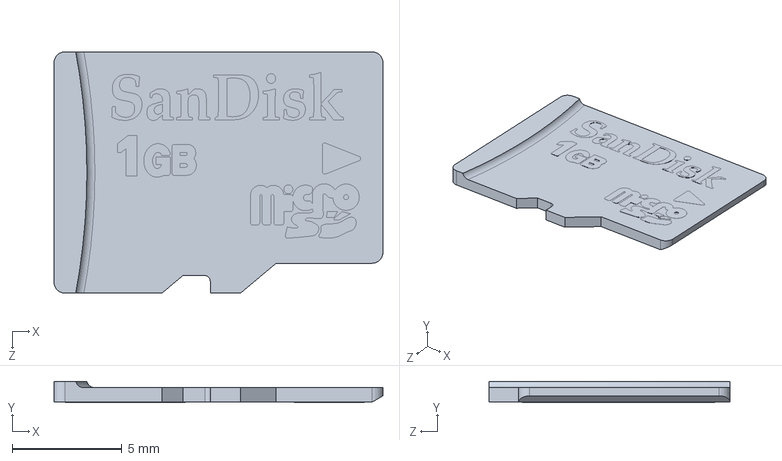
[picture p171: CAD file, 2017-04-19]
Weighing Machine Design/rpi/raspberry_pi_B+_(microsd2).SLDPRT
15.0 x 0.975 x 11.0 mm
