Parin810/Farm-Produce-Logging-and-Monitoring-/Weighing Machine Design/rpi/raspberry_pi__HDMI_socket_large_pin.SLDPRT

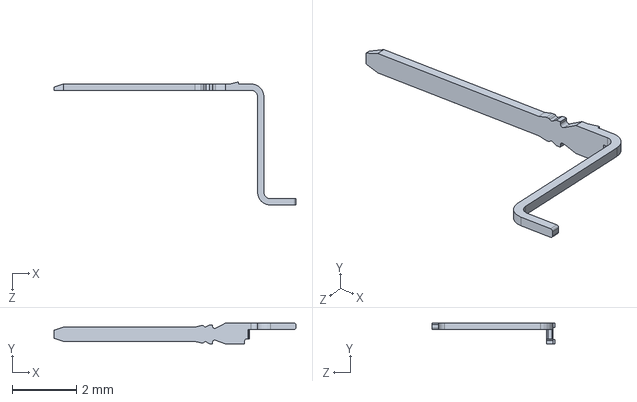
[picture p172: CAD file, 2017-04-19]
Weighing Machine Design/rpi/raspberry_pi__HDMI_socket_large_pin.SLDPRT
7.55 x 0.65 x 3.84 mm
