Parin810/Farm-Produce-Logging-and-Monitoring-/Weighing Machine Design/rpi/raspberry_pi_B+_(QFN64).SLDPRT

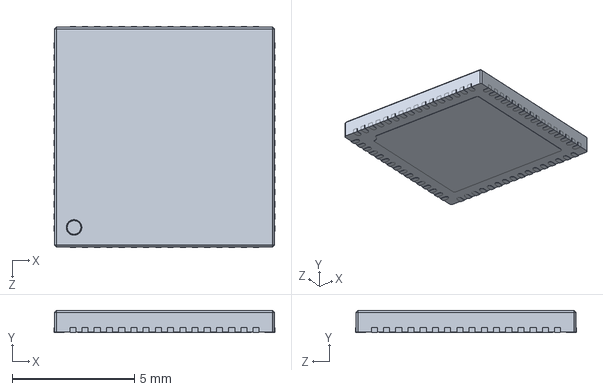
[picture p173: CAD file, 2017-04-19]
Weighing Machine Design/rpi/raspberry_pi_B+_(QFN64).SLDPRT
9.04 x 0.9 x 9.04 mm
