Parin810/Farm-Produce-Logging-and-Monitoring-/Weighing Machine Design/WeighingPlateform.SLDPRT

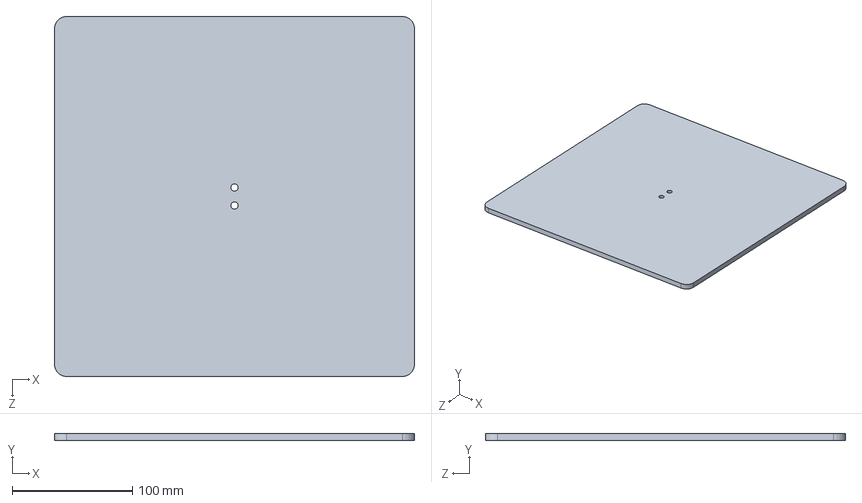
[picture p174: CAD file, 2017-04-19]
Weighing Machine Design/WeighingPlateform.SLDPRT
300.0 x 6.00 x 300.0 mm
