Parin810/Farm-Produce-Logging-and-Monitoring-/Weighing Machine Design/rpi/raspberry_pi_B+_(bar_180_2x20).SLDPRT

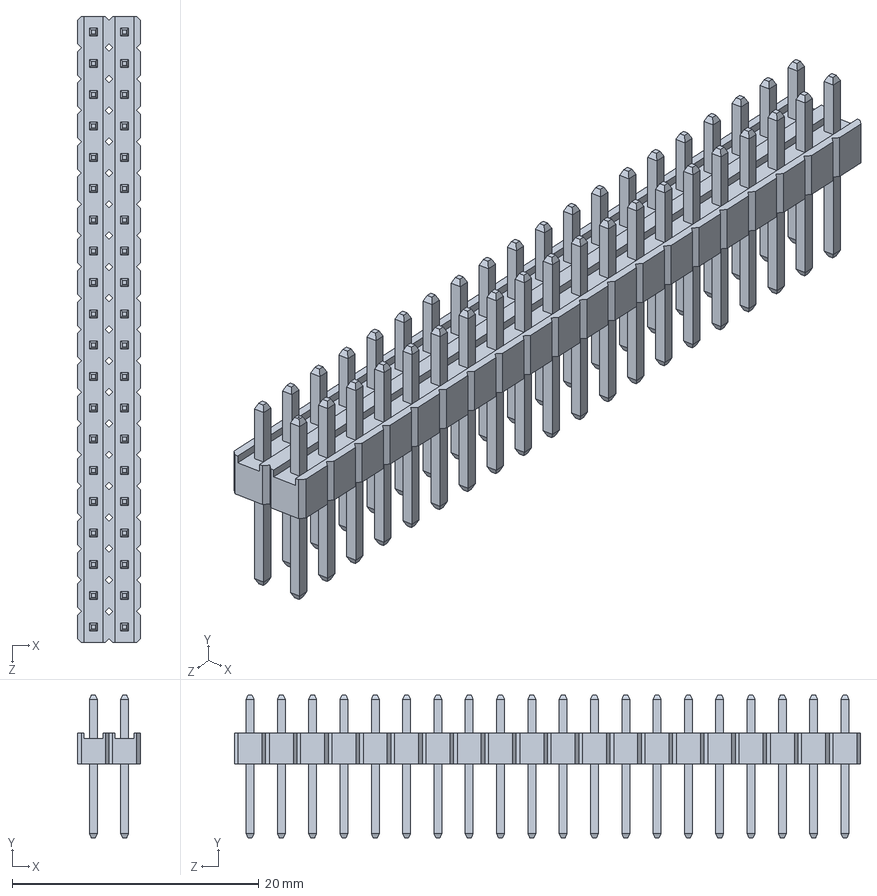
[picture p175: CAD file, 2017-04-19]
Weighing Machine Design/rpi/raspberry_pi_B+_(bar_180_2x20).SLDPRT
5.08 x 11.6 x 50.8 mm
