Parin810/Farm-Produce-Logging-and-Monitoring-/Weighing Machine Design/rpi/raspberry_pi__15_pin_FFC_Connector_pins.SLDPRT

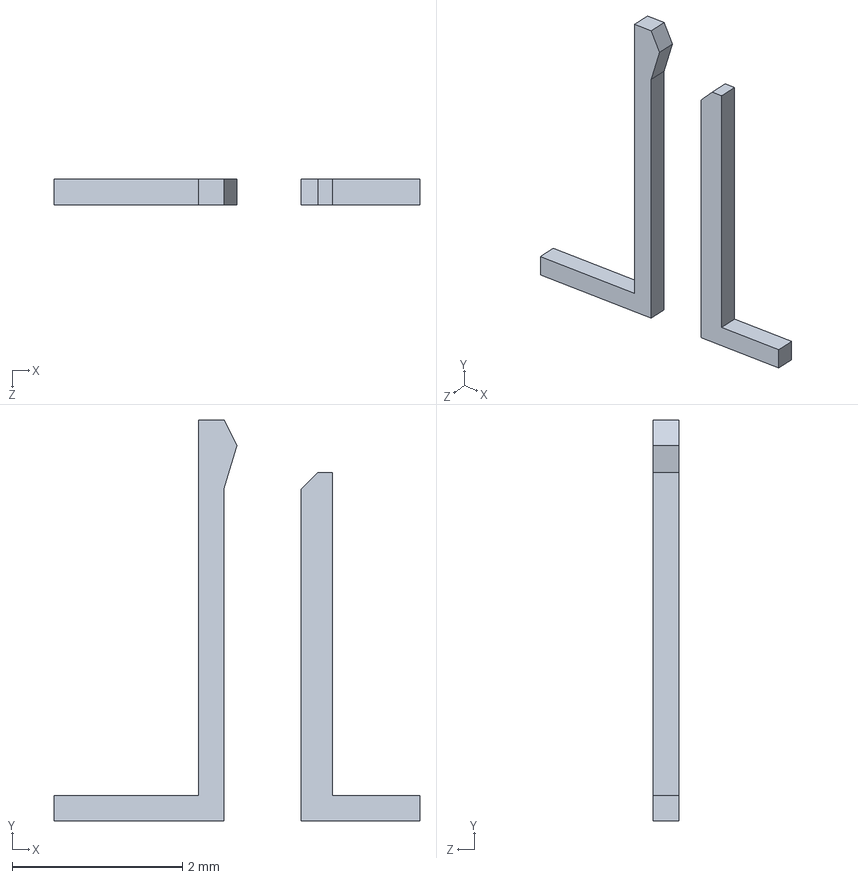
[picture p176: CAD file, 2017-04-19]
Weighing Machine Design/rpi/raspberry_pi__15_pin_FFC_Connector_pins.SLDPRT
4.30 x 4.71 x 0.3 mm
