Parin810/Farm-Produce-Logging-and-Monitoring-/Weighing Machine Design/cylinder.SLDPRT

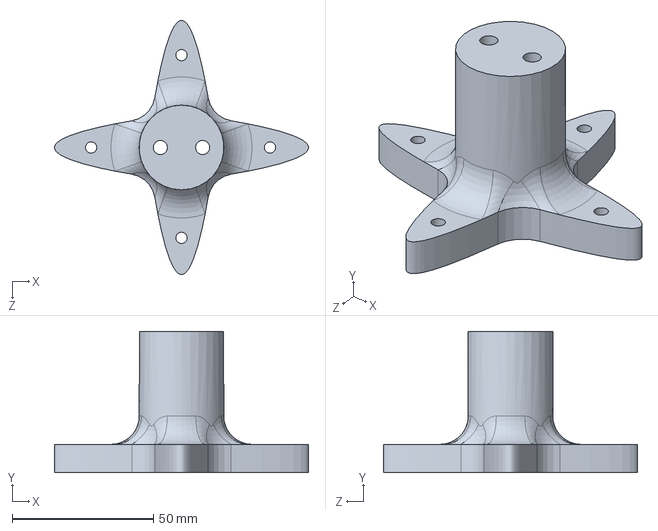
[picture p177: CAD file, 2017-04-19]
Weighing Machine Design/cylinder.SLDPRT
90.0 x 50.0 x 90.0 mm
