Parin810/Farm-Produce-Logging-and-Monitoring-/Weighing Machine Design/rpi/raspberry_pi__15_pin_FFC_Connector_locker.SLDPRT

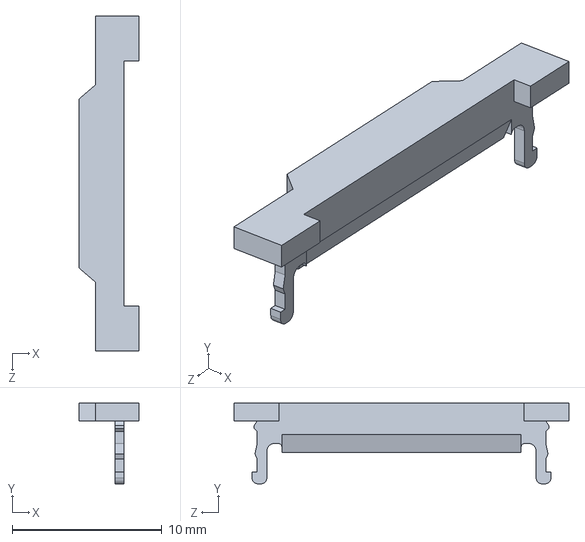
[picture p178: CAD file, 2017-04-19]
Weighing Machine Design/rpi/raspberry_pi__15_pin_FFC_Connector_locker.SLDPRT
4.00 x 5.40 x 22.4 mm
