Parin810/Farm-Produce-Logging-and-Monitoring-/Weighing Machine Design/feet.SLDPRT

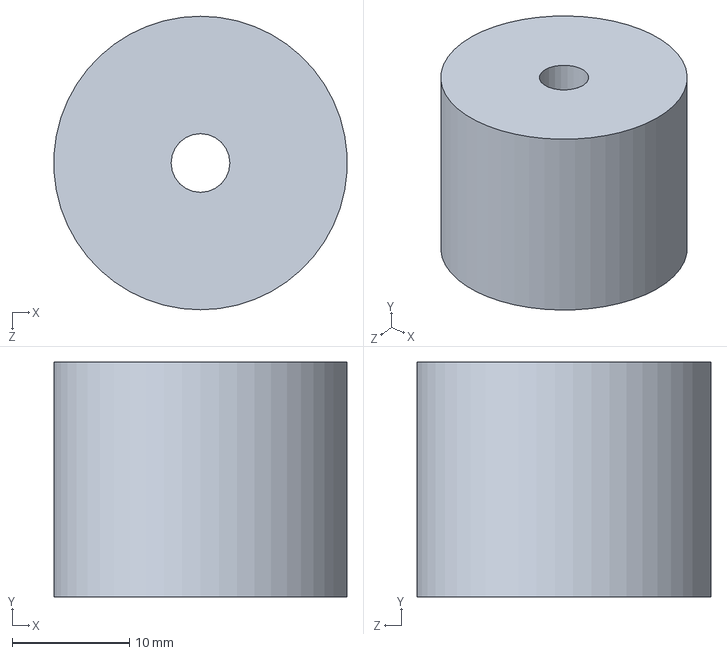
[picture p179: CAD file, 2017-04-19]
Weighing Machine Design/feet.SLDPRT
25.0 x 20.0 x 25.0 mm
