Parin810/Farm-Produce-Logging-and-Monitoring-/Weighing Machine Design/rpi/raspberry_pi__HDMI_socket_inside.SLDPRT

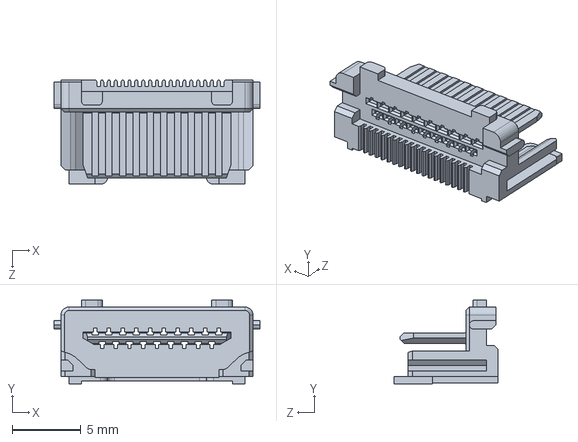
[picture p180: CAD file, 2017-04-19]
Weighing Machine Design/rpi/raspberry_pi__HDMI_socket_inside.SLDPRT
15.0 x 6.10 x 7.60 mm
