Parin810/Farm-Produce-Logging-and-Monitoring-/Weighing Machine Design/baseplate.SLDPRT

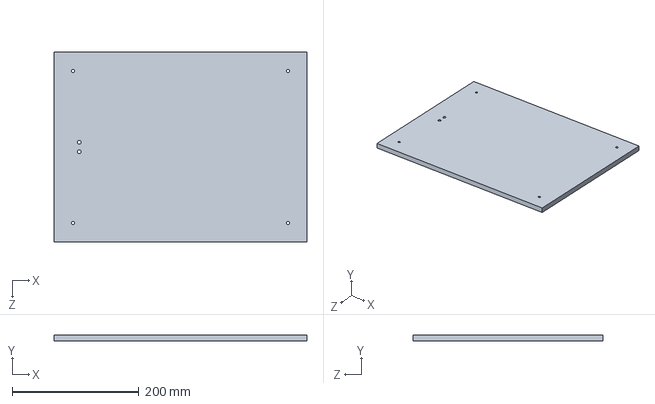
[picture p181: CAD file, 2017-04-19]
Weighing Machine Design/baseplate.SLDPRT
400.0 x 10.0 x 300.0 mm
