Parin810/Farm-Produce-Logging-and-Monitoring-/Weighing Machine Design/rpi/raspberry_pi_B+_(micro_USB_cover).SLDPRT

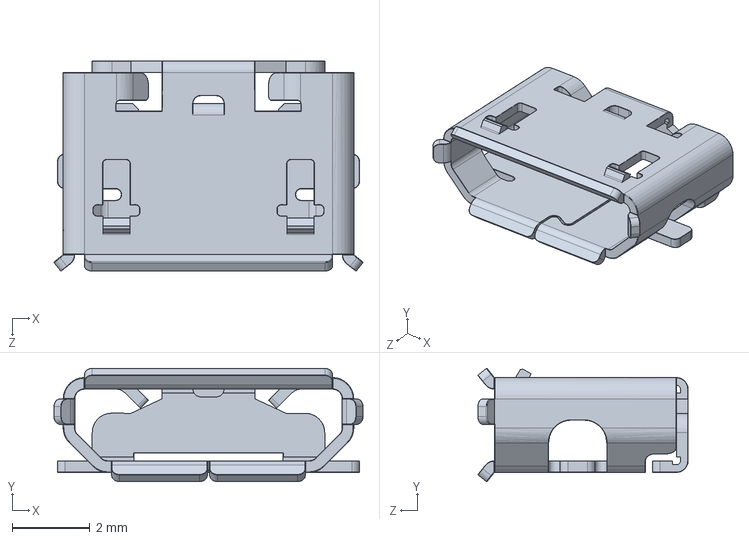
[picture p182: CAD file, 2017-04-19]
Weighing Machine Design/rpi/raspberry_pi_B+_(micro_USB_cover).SLDPRT
7.97 x 2.92 x 5.43 mm
