Parin810/Farm-Produce-Logging-and-Monitoring-/Weighing Machine Design/rpi/raspberry_pi_B+_(microsd_slot2).SLDPRT

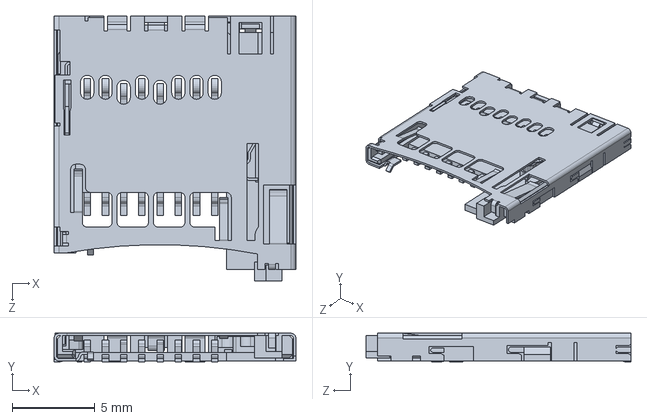
[picture p183: CAD file, 2017-04-19]
Weighing Machine Design/rpi/raspberry_pi_B+_(microsd_slot2).SLDPRT
14.6 x 1.73 x 16.0 mm
