Parin810/Farm-Produce-Logging-and-Monitoring-/Weighing Machine Design/topplate.SLDPRT

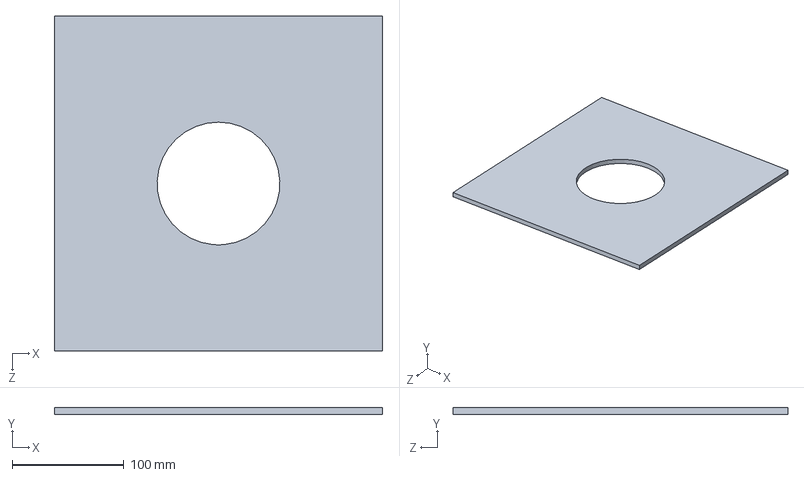
[picture p184: CAD file, 2017-04-19]
Weighing Machine Design/topplate.SLDPRT
294.0 x 6.00 x 300.0 mm
