Parin810/Farm-Produce-Logging-and-Monitoring-/Weighing Machine Design/Middleplate.SLDPRT

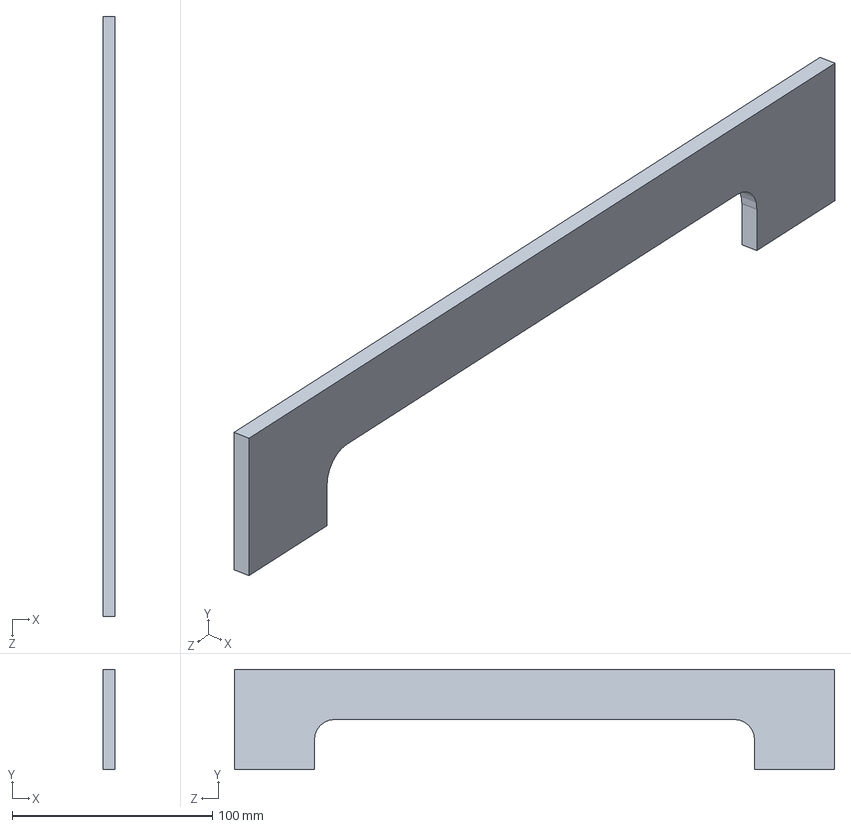
[picture p185: CAD file, 2017-04-19]
Weighing Machine Design/Middleplate.SLDPRT
6.00 x 50.0 x 300.0 mm
