Parin810/Farm-Produce-Logging-and-Monitoring-/Weighing Machine Design/BackPlate.SLDPRT

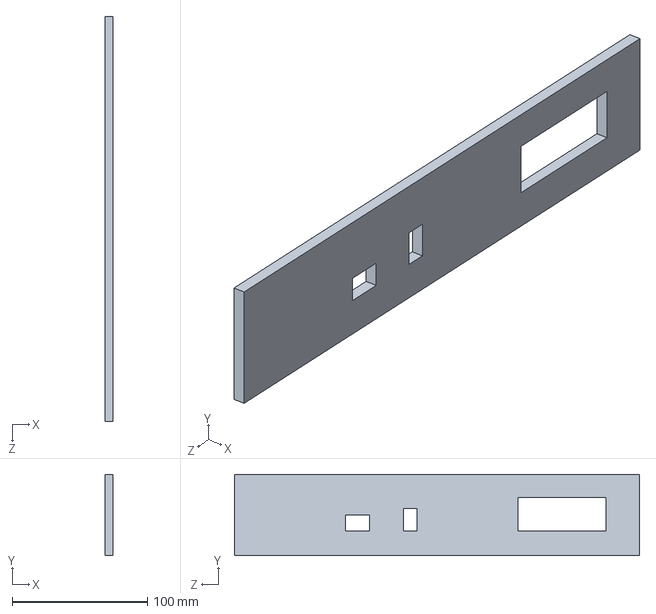
[picture p186: CAD file, 2017-04-19]
Weighing Machine Design/BackPlate.SLDPRT
6.00 x 60.0 x 300.0 mm
