Parin810/Farm-Produce-Logging-and-Monitoring-/Weighing Machine Design/cncdimensiion.SLDPRT

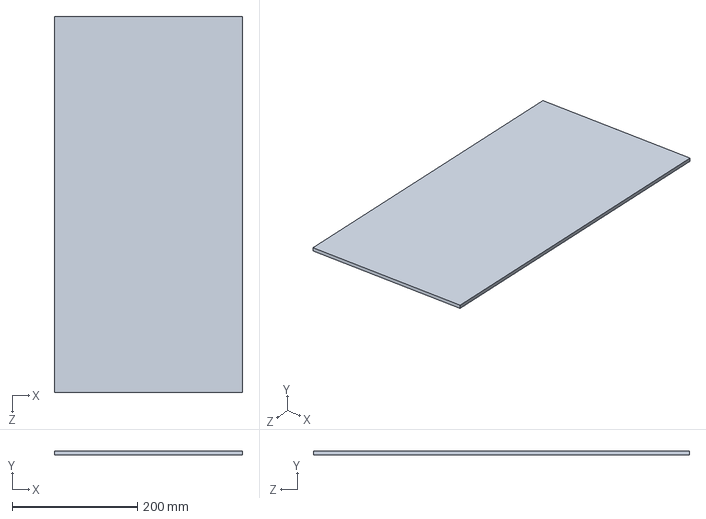
[picture p187: CAD file, 2017-04-19]
Weighing Machine Design/cncdimensiion.SLDPRT
300.0 x 6.00 x 600.0 mm
