Parin810/Farm-Produce-Logging-and-Monitoring-/Weighing Machine Design/frontplate.SLDPRT

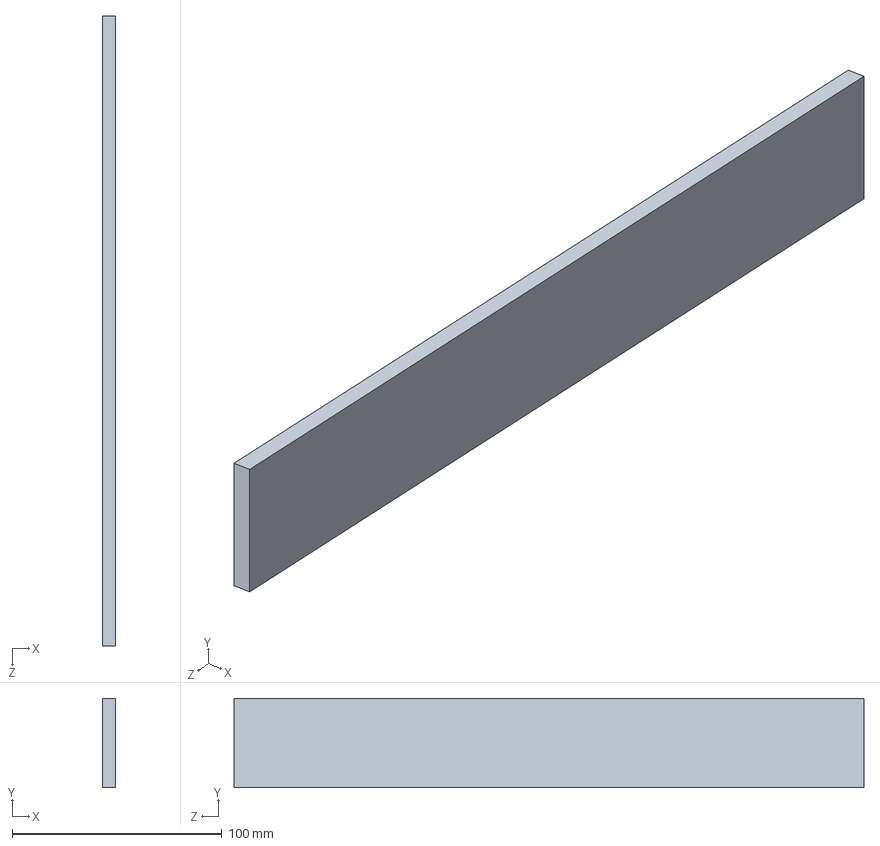
[picture p188: CAD file, 2017-04-19]
Weighing Machine Design/frontplate.SLDPRT
6.00 x 42.5 x 300.0 mm
