Parin810/Farm-Produce-Logging-and-Monitoring-/Weighing Machine Design/rpi/raspberry_pi_B+_(USB_x2_part1).SLDPRT

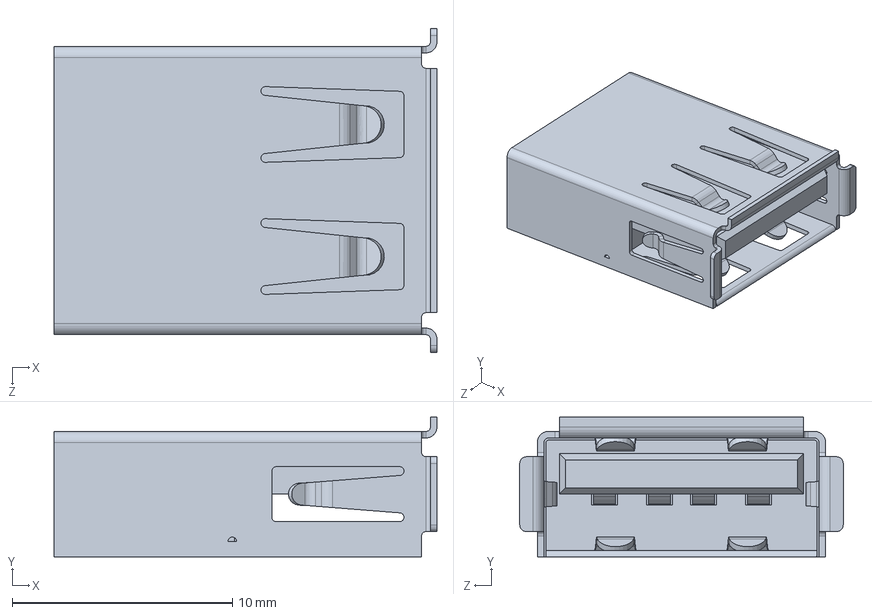
[picture p189: CAD file, 2017-04-19]
Weighing Machine Design/rpi/raspberry_pi_B+_(USB_x2_part1).SLDPRT
17.4 x 6.35 x 14.7 mm
