Parin810/Farm-Produce-Logging-and-Monitoring-/Weighing Machine Design/rpi/raspberry_pi_B+_(USB_x2_part2).SLDPRT

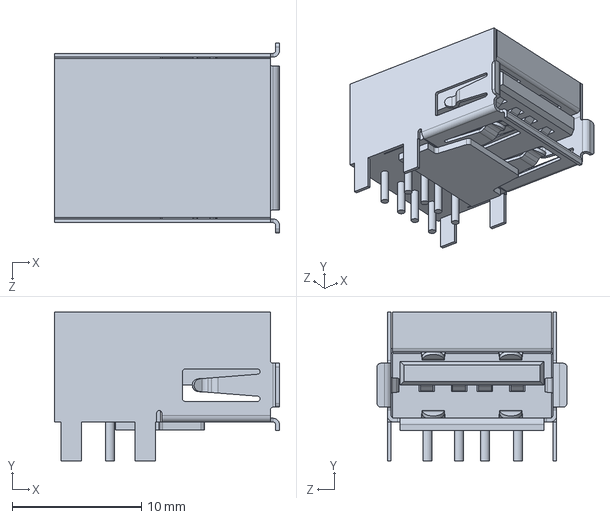
[picture p190: CAD file, 2017-04-19]
Weighing Machine Design/rpi/raspberry_pi_B+_(USB_x2_part2).SLDPRT
17.4 x 11.5 x 14.7 mm
