Parin810/Farm-Produce-Logging-and-Monitoring-/Weighing Machine Design/rpi/raspberry_pi_B+_(micro_USB_contacts).SLDPRT

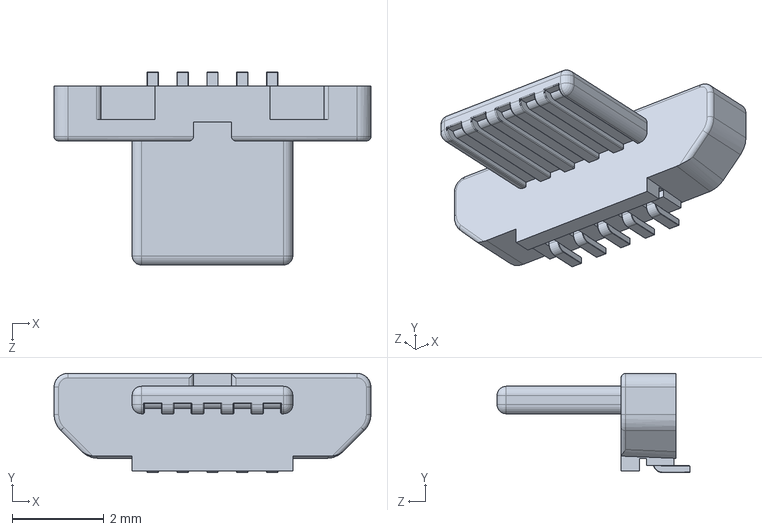
[picture p191: CAD file, 2017-04-19]
Weighing Machine Design/rpi/raspberry_pi_B+_(micro_USB_contacts).SLDPRT
6.90 x 2.16 x 4.20 mm
