Parin810/Farm-Produce-Logging-and-Monitoring-/Weighing Machine Design/rpi/raspberry_pi__15_pin_FFC_Connector_body.SLDPRT

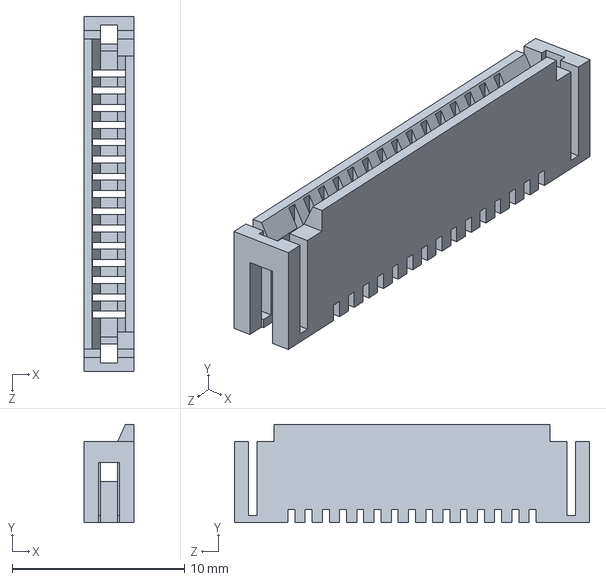
[picture p192: CAD file, 2017-04-19]
Weighing Machine Design/rpi/raspberry_pi__15_pin_FFC_Connector_body.SLDPRT
2.90 x 5.70 x 20.6 mm
