Parin810/Farm-Produce-Logging-and-Monitoring-/Weighing Machine Design/rpi/raspberry_pi__HDMI_socket_cover.SLDPRT

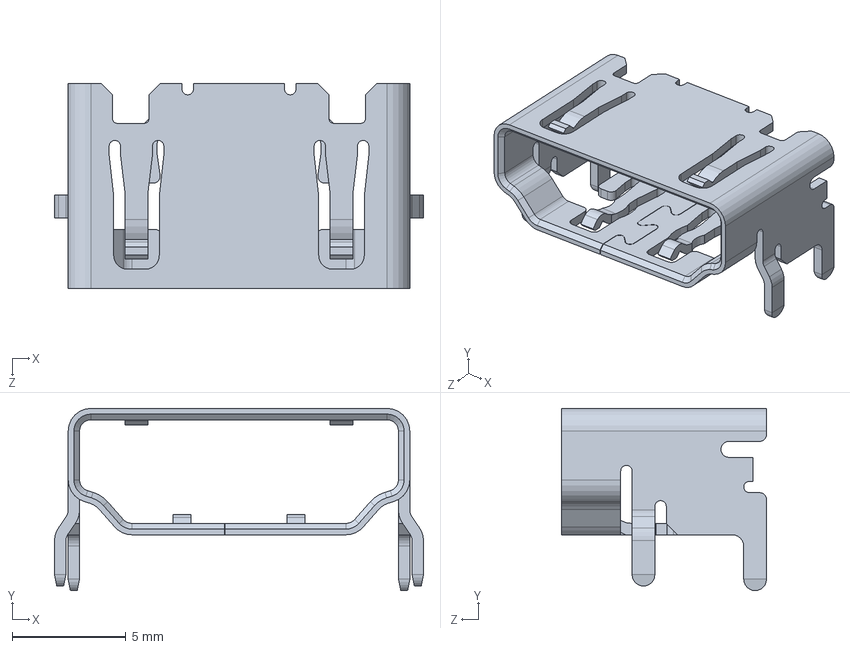
[picture p193: CAD file, 2017-04-19]
Weighing Machine Design/rpi/raspberry_pi__HDMI_socket_cover.SLDPRT
16.2 x 8.00 x 9.00 mm
